Dargonrol/processor-dev/Dragon/Dragon_4/Software/TommyPROM-master/docs/images/TommyPROM-pcb-with-ui.jpg

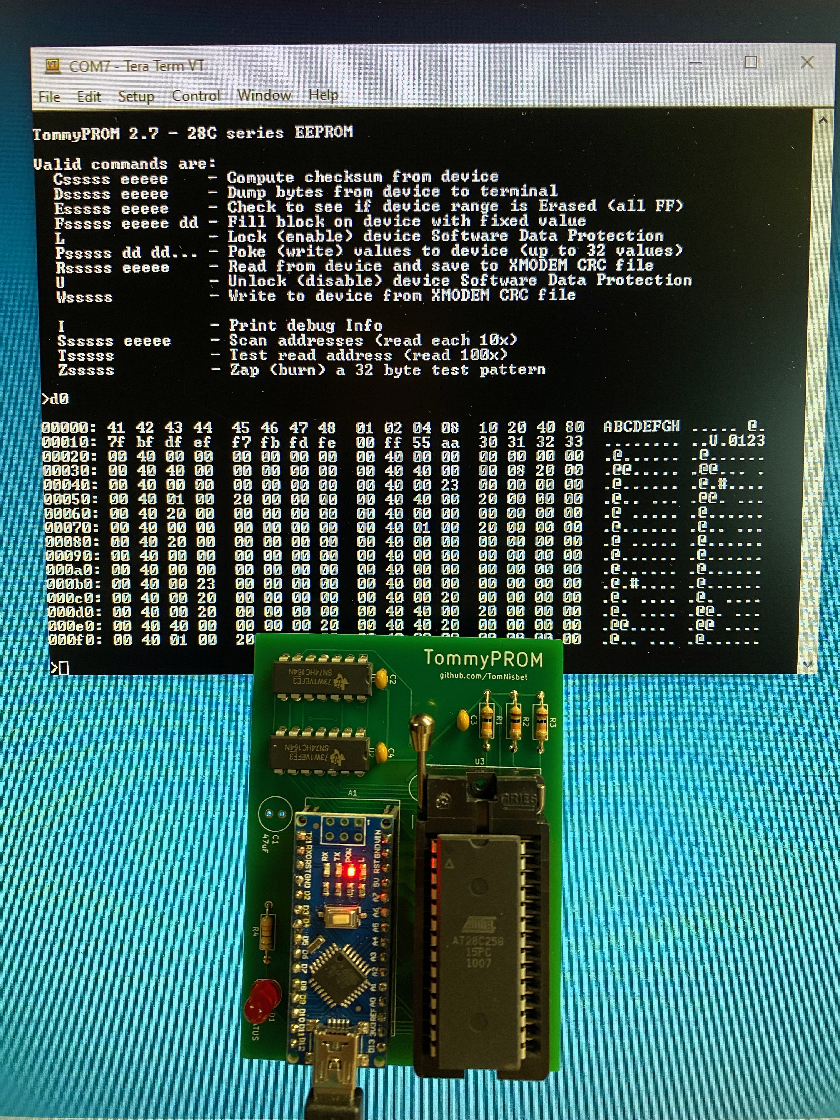
Dragon/Dragon_4/Software/TommyPROM-master/docs/images/TommyPROM-pcb-with-ui.jpg
