Dargonrol/processor-dev/Dragon/Dragon_2/Dragon-2_Microachitecture.JPG

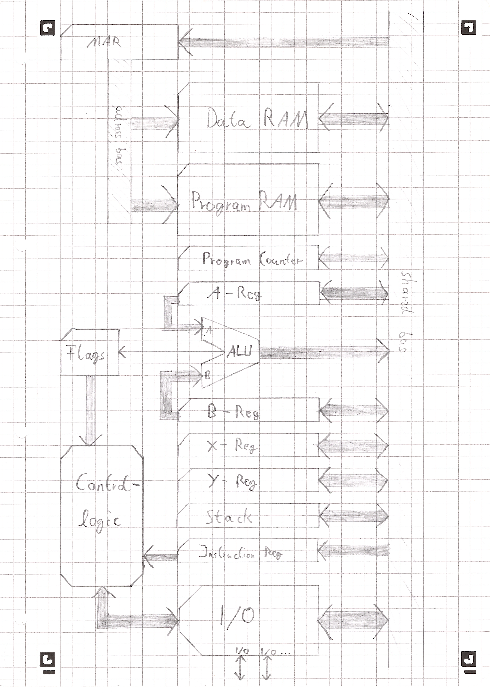
Dragon/Dragon_2/Dragon-2_Microachitecture.JPG
