Dargonrol/processor-dev/Dragon/Dragon_4/Jugend Forscht/Jugend Forscht/Clk-code_screenshot.png

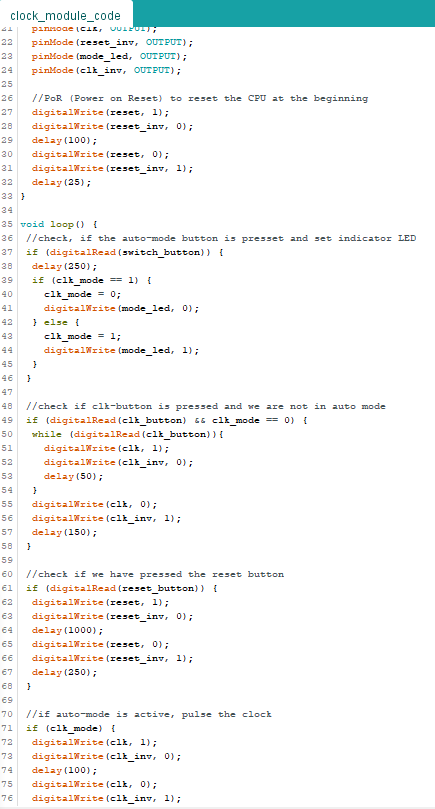
Dragon/Dragon_4/Jugend Forscht/Jugend Forscht/Clk-code_screenshot.png
