Dargonrol/processor-dev/Dragon/Dragon_4/Jugend Forscht/Jugend Forscht/Control-Logic_board_screenshot.png

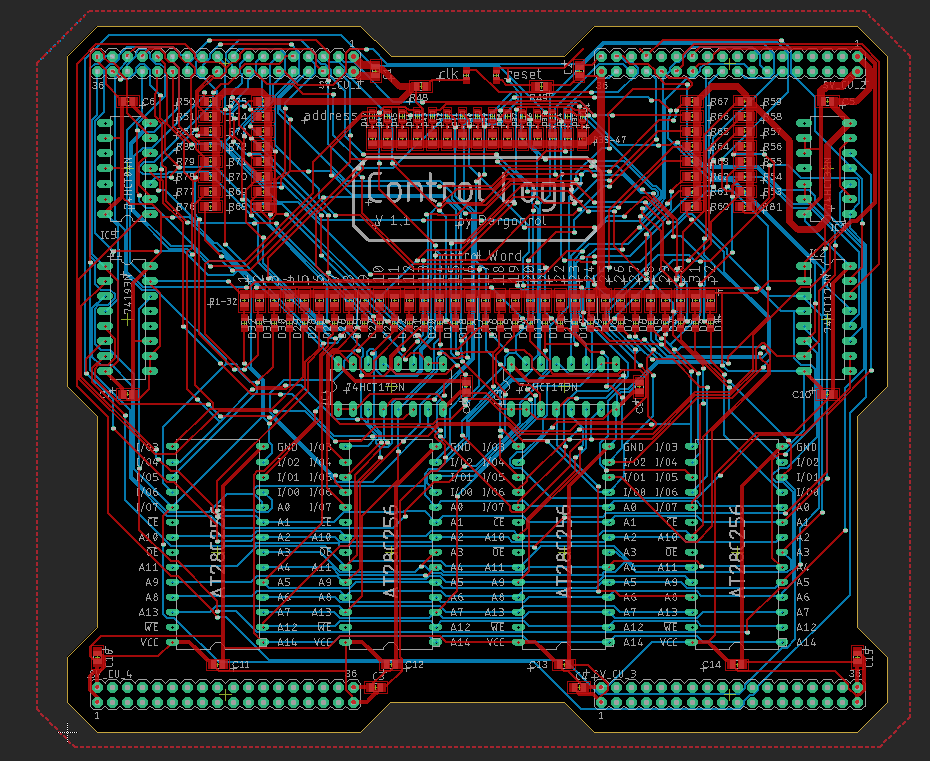
Dragon/Dragon_4/Jugend Forscht/Jugend Forscht/Control-Logic_board_screenshot.png
