Dargonrol/processor-dev/Dragon/Dragon_4/Jugend Forscht/Jugend Forscht/Hex-Editor_screenshot.png

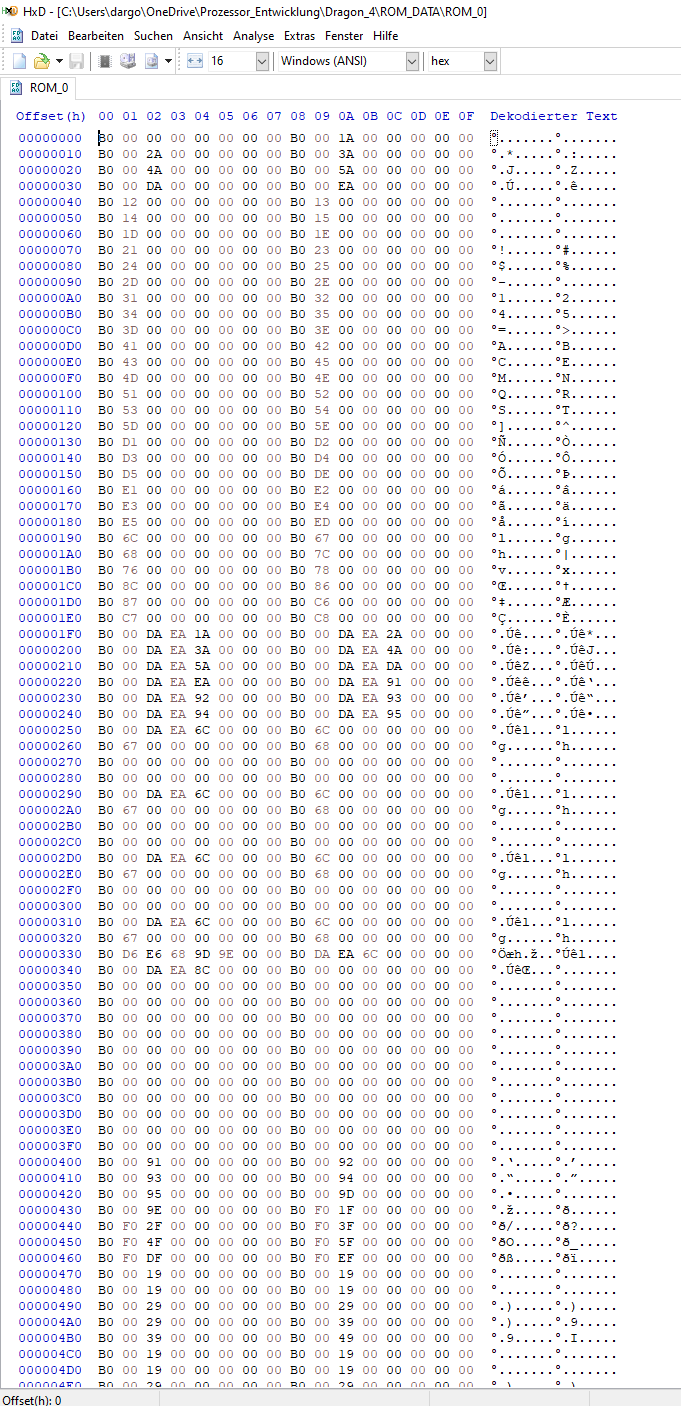
Dragon/Dragon_4/Jugend Forscht/Jugend Forscht/Hex-Editor_screenshot.png
