Dargonrol/processor-dev/Dragon/Dragon_4/Jugend Forscht/Jugend Forscht/logic-simulation_screenshot.png

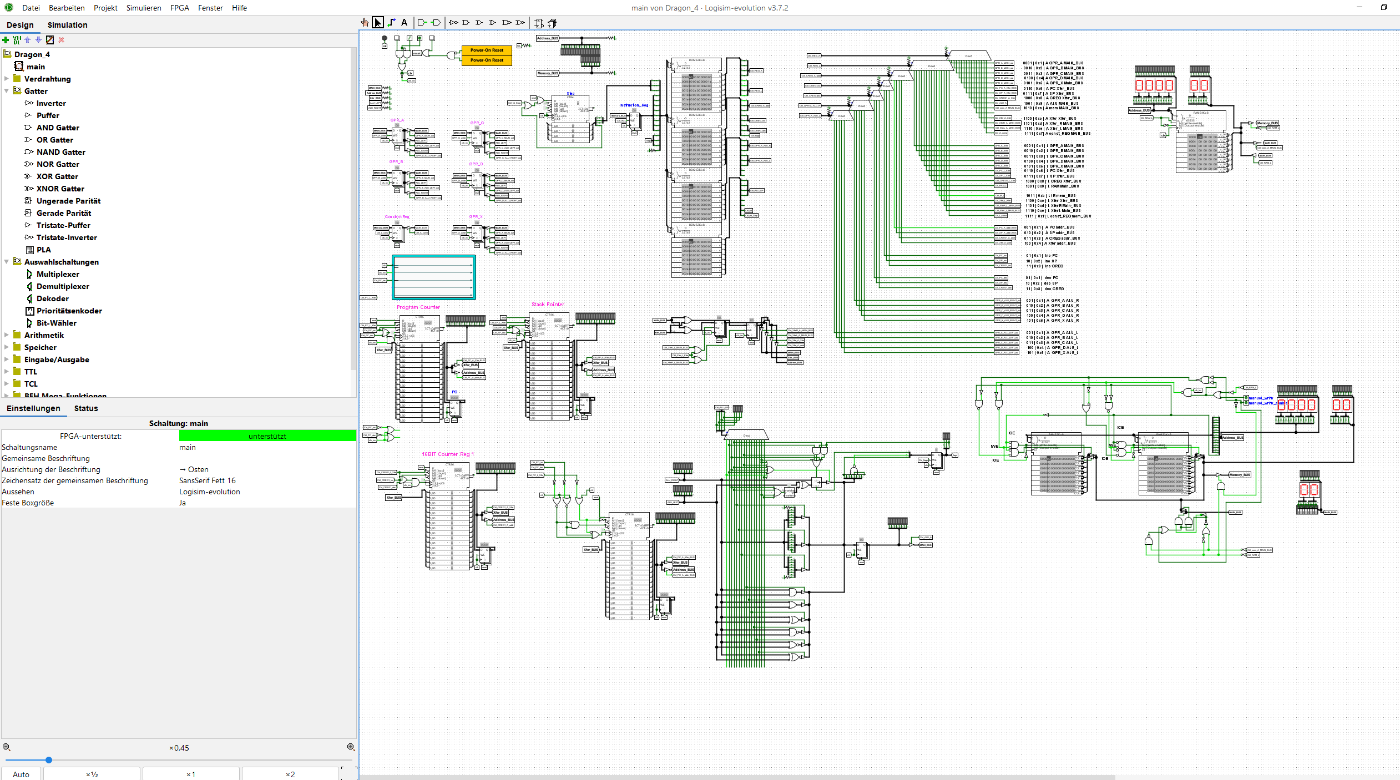
Dragon/Dragon_4/Jugend Forscht/Jugend Forscht/logic-simulation_screenshot.png
