Dargonrol/processor-dev/Dragon/Dragon_4/Jugend Forscht/Jugend Forscht/ROM-Code-gen_1_screenshot.png

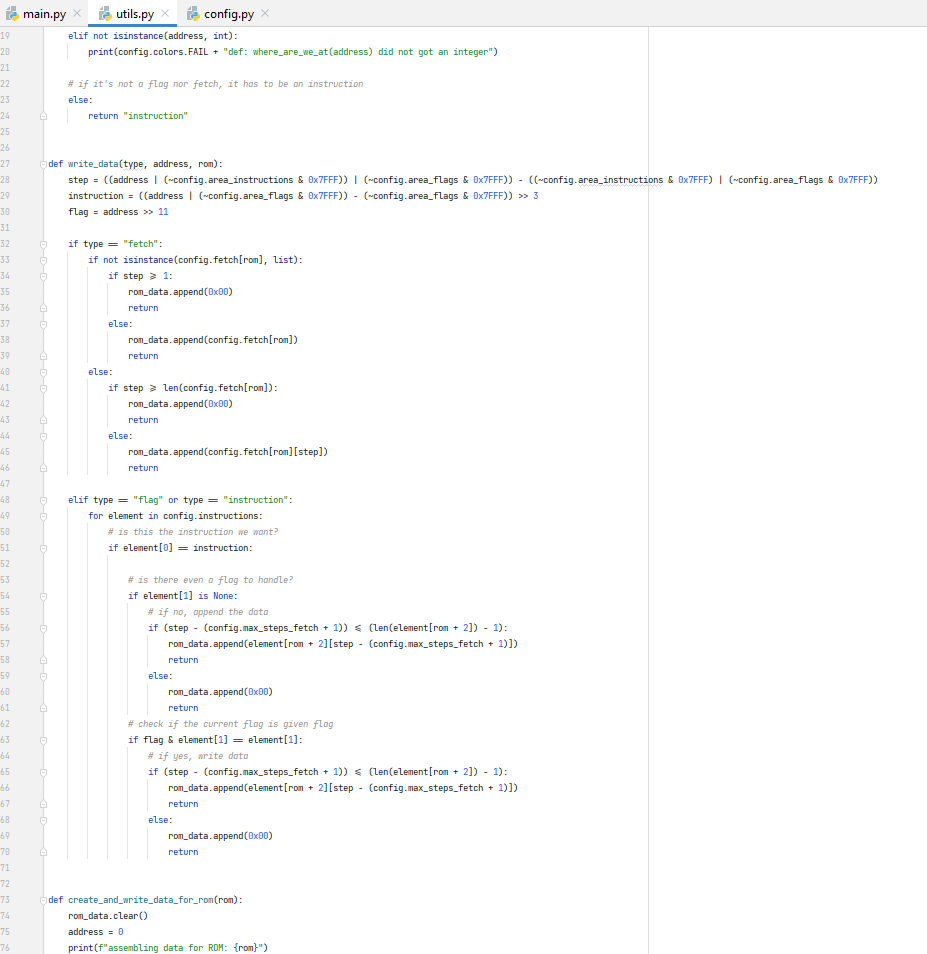
Dragon/Dragon_4/Jugend Forscht/Jugend Forscht/ROM-Code-gen_1_screenshot.png
