Dargonrol/processor-dev/Dragon/Dragon_4/Jugend Forscht/Jugend Forscht/Tera-Term_screenshot.png

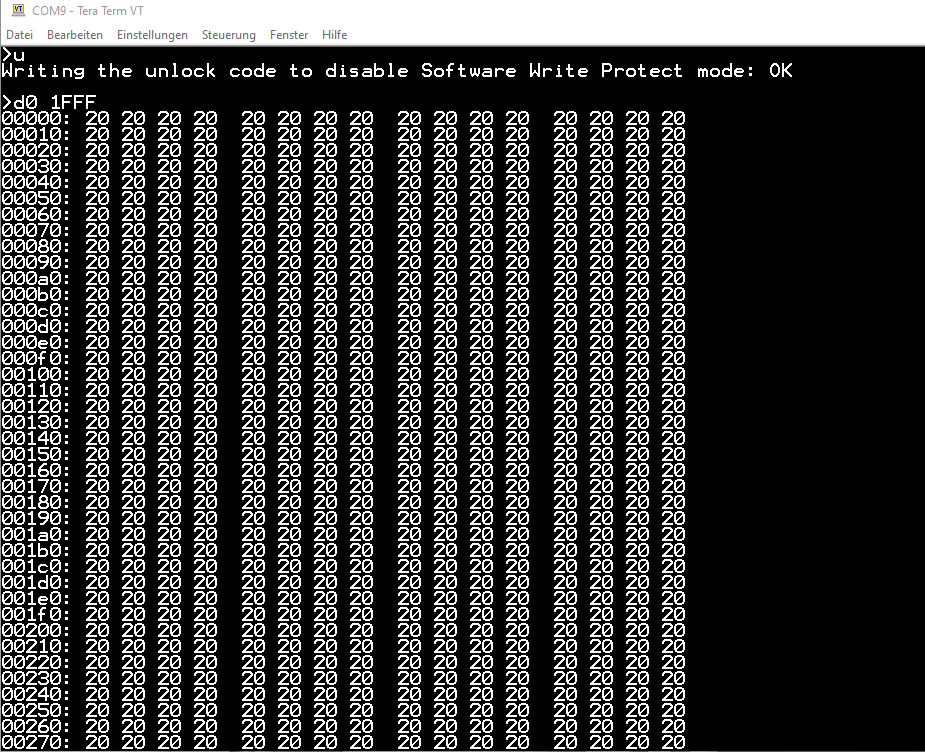
Dragon/Dragon_4/Jugend Forscht/Jugend Forscht/Tera-Term_screenshot.png
