Dargonrol/processor-dev/Dragon/Dragon_4/Software/Control_Logic_Data_generator/temp_screen_1.png

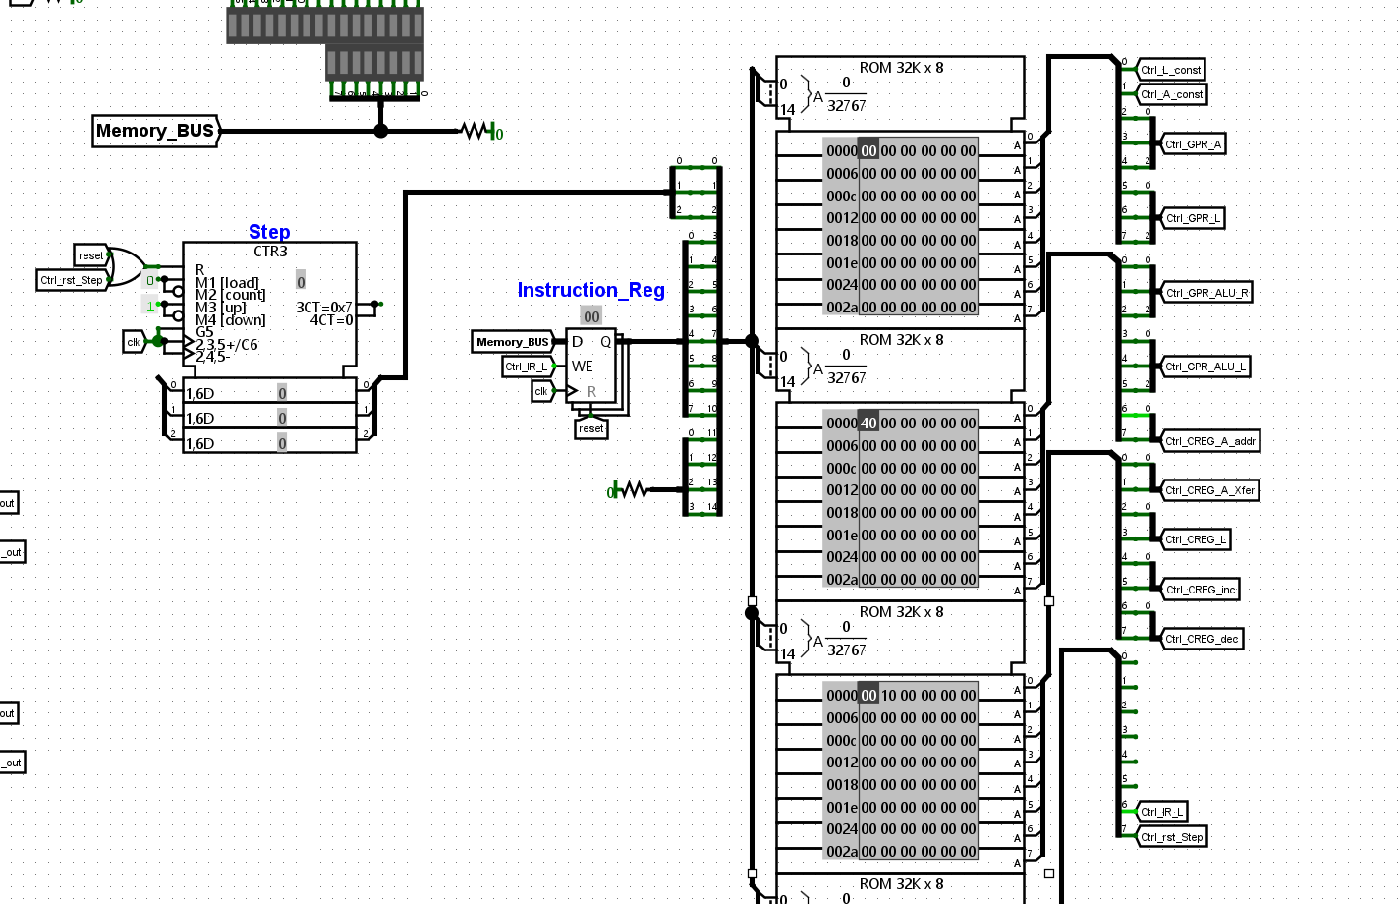
Dragon/Dragon_4/Software/Control_Logic_Data_generator/temp_screen_1.png
