Dargonrol/processor-dev/Dragon/Dragon_4/Jugend Forscht/Jugend Forscht/part_of_instruction-set_definition_screenshot.png

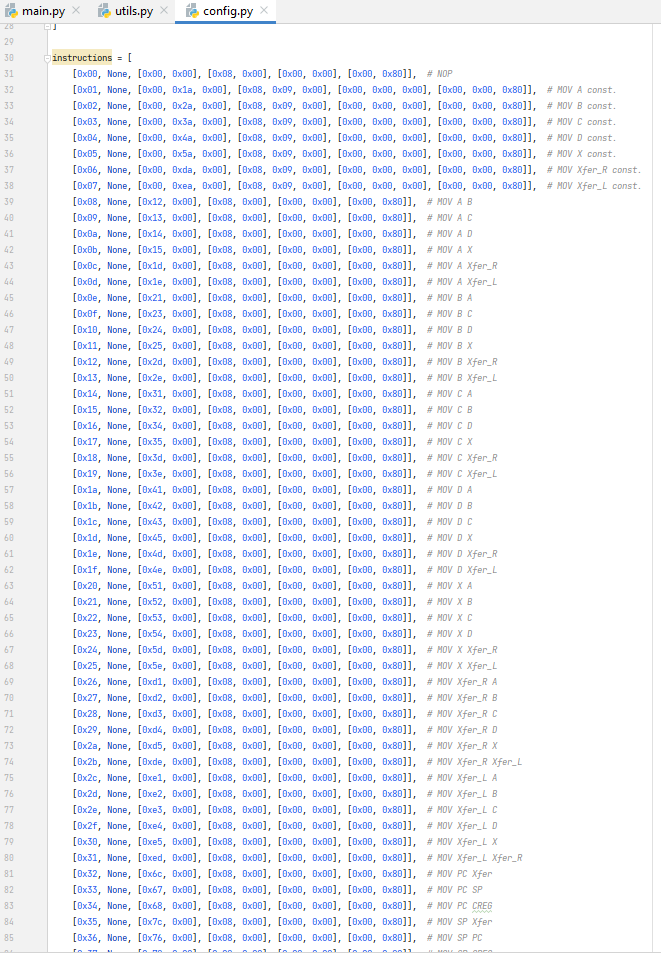
Dragon/Dragon_4/Jugend Forscht/Jugend Forscht/part_of_instruction-set_definition_screenshot.png
