Dargonrol/processor-dev/Dragon/Dragon_4/PCBs/Control Logic/Control_Logic_V2.brd

## EAGLE design Dragon/Dragon_4/PCBs/Control Logic/Control_Logic_V2.brd (2025-08-28)

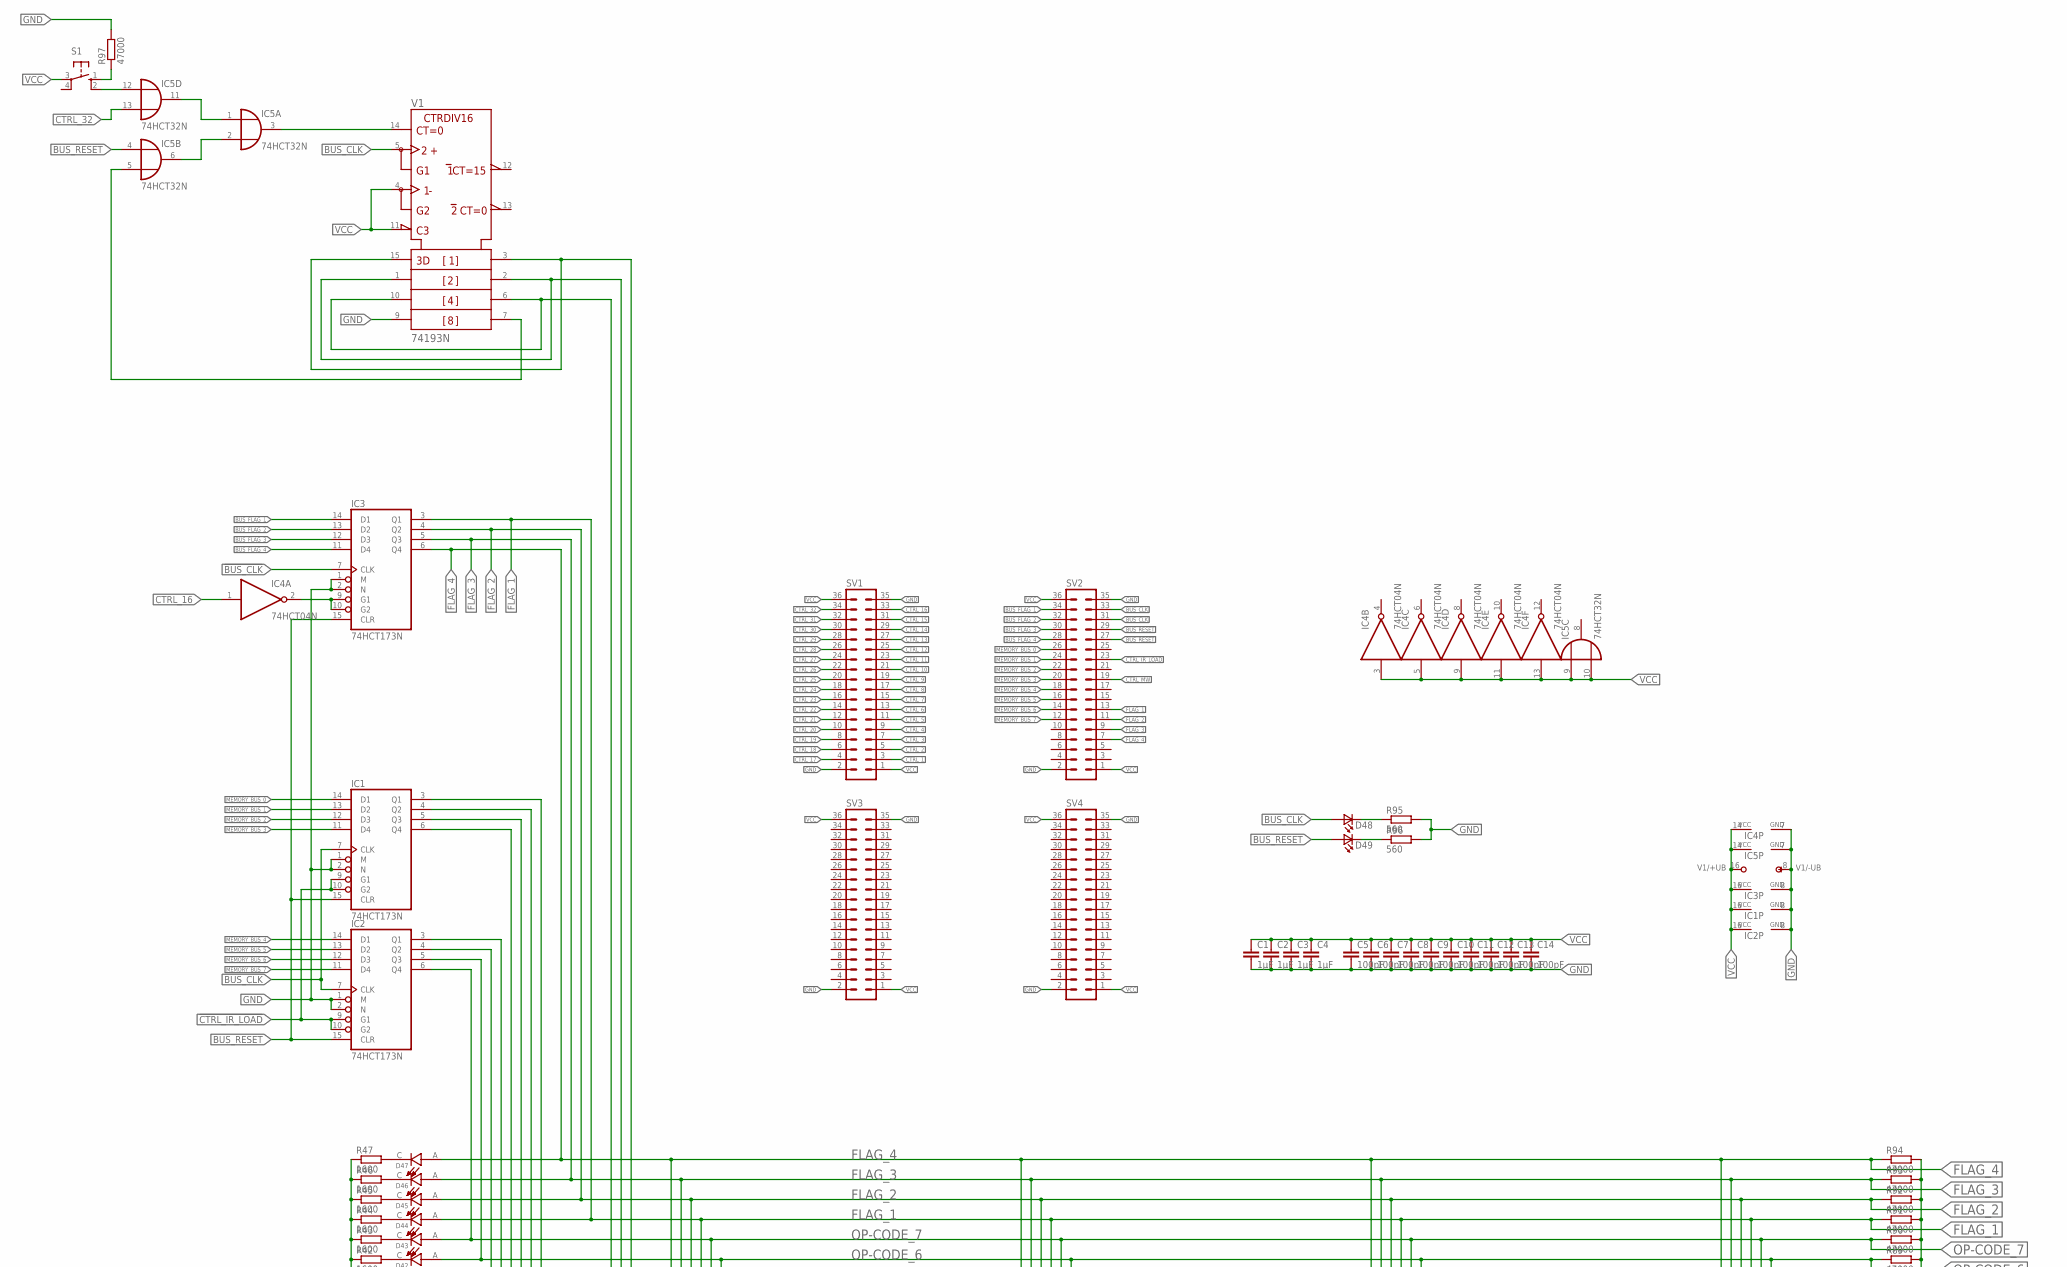
[picture p90: schematic Control_Logic_V2.sch, part in row 1, column 1]

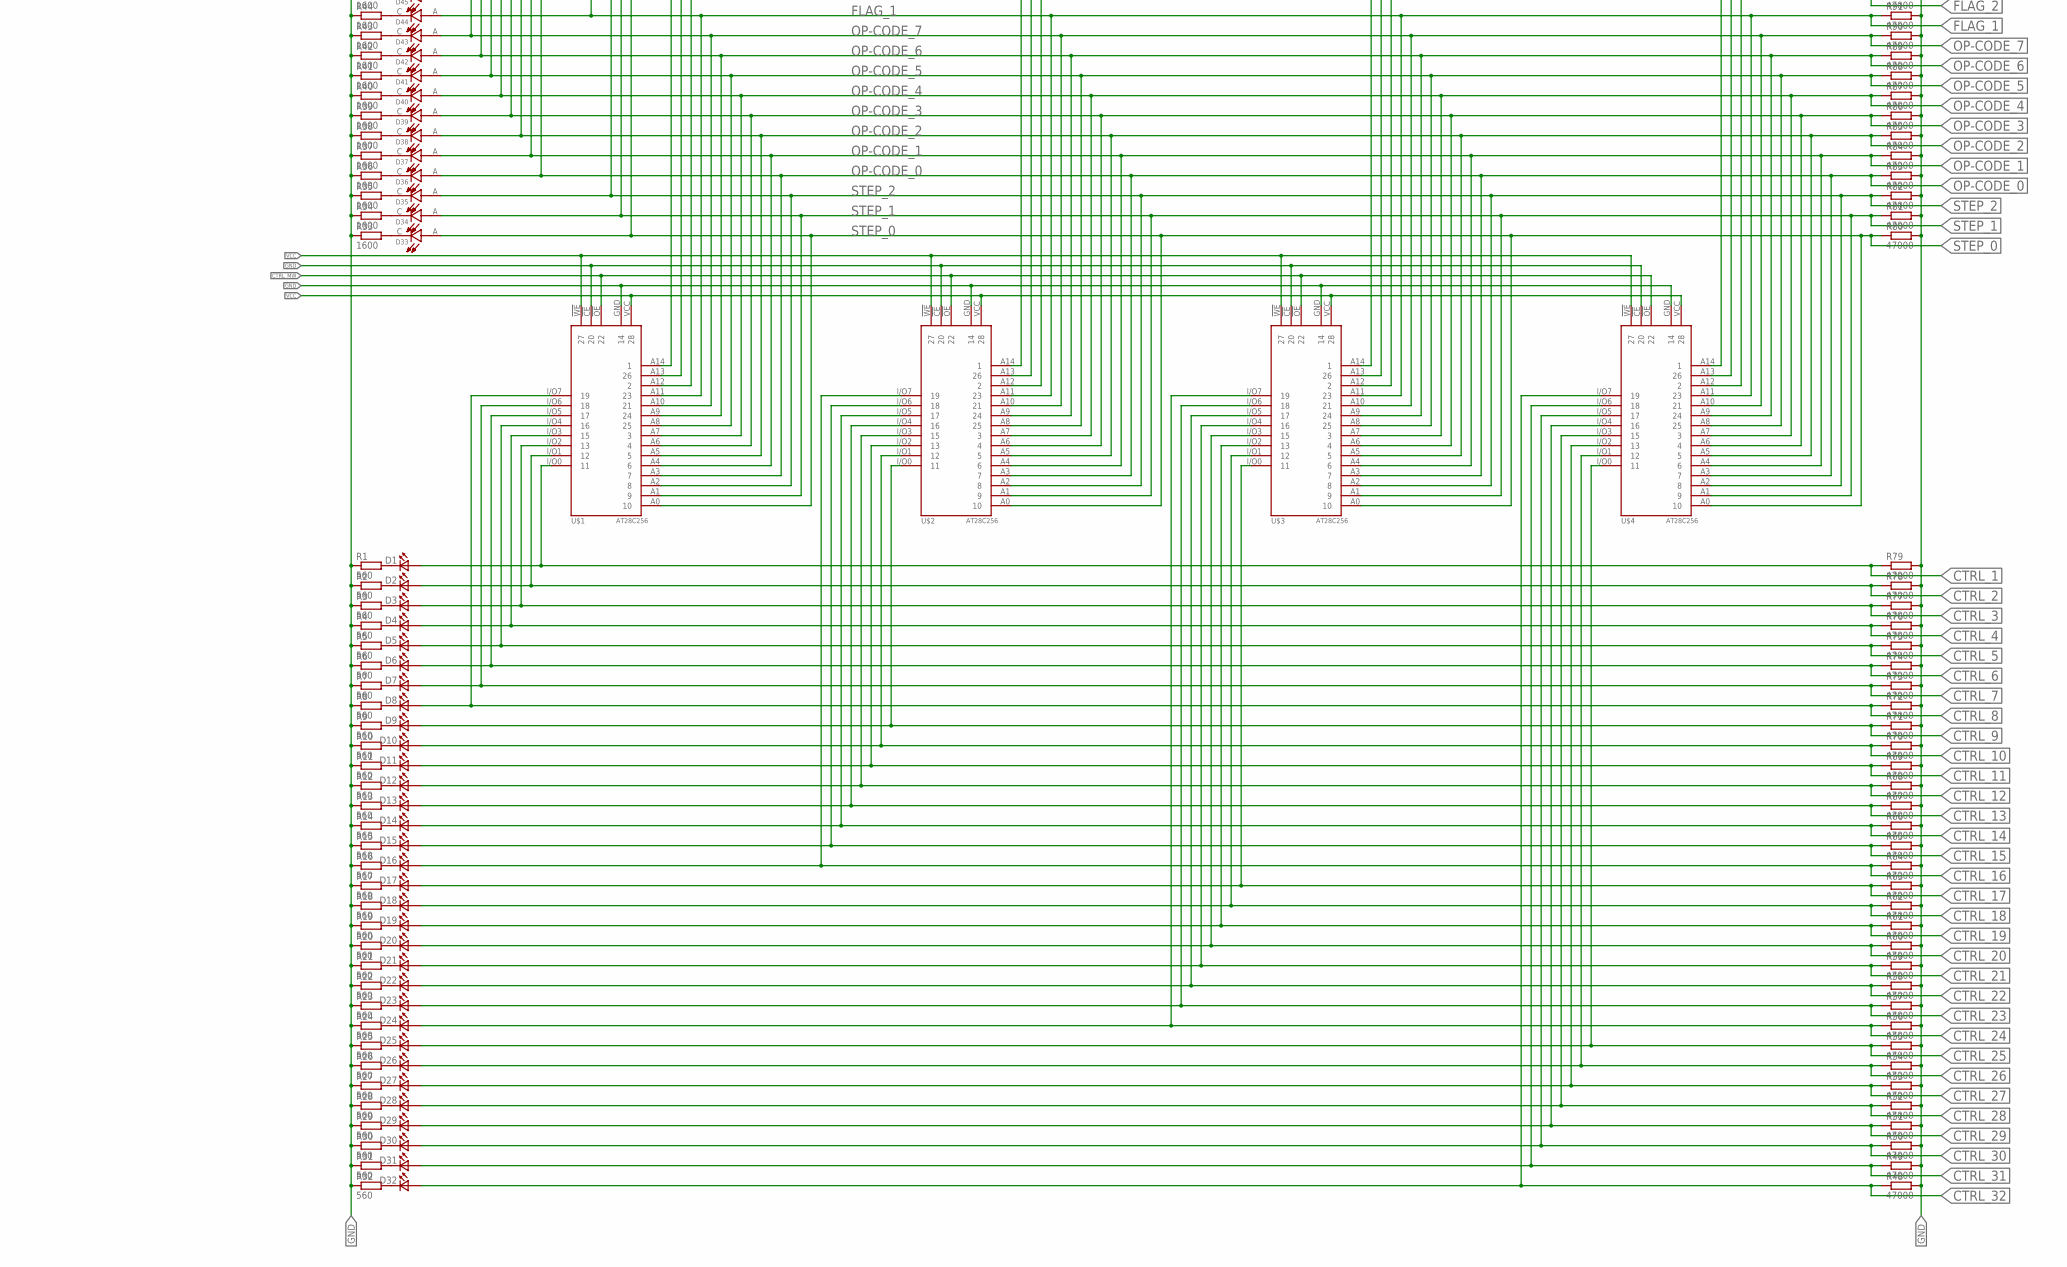
[picture p91: schematic Control_Logic_V2.sch, part in row 2, column 1]

Parts:
C1, C2, C3, C4: 1µF; C0805
C5, C6, C7, C8, C9, C10, C11, C12, C13, C14: 100pF; C0805
D1, D2, D3, D4, D5, D6, D7, D8, D9, D10, D11, D12, D13, D14, D15, D16, D17, D18, D19, D20, D21, D22, D23, D24, D25, D26, D27, D28, D29, D30, D31, D32, D48, D49: LTST-C193TBKT-5A; 0603
D33, D34, D35, D36, D37, D38, D39, D40, D41, D42, D43, D44, D45, D46, D47: LTST-C193KRKT-5A; LEDC1608X45N
IC1, IC2, IC3: 74HCT173N; DIL16
IC4: 74HCT04N; DIL14
IC5: 74HCT32N; DIL14
R1, R2, R3, R4, R5, R6, R7, R8, R9, R10, R11, R12, R13, R14, R15, R16, R17, R18, R19, R20, R21, R22, R23, R24, R25, R26, R27, R28, R29, R30, R31, R32, R95, R96: 560; R0805
R33, R34, R35, R36, R37, R38, R39, R40, R41, R42, R43, R44, R45, R46, R47: 1600; R0805
R48, R49, R50, R51, R52, R53, R54, R55, R56, R57, R58, R59, R60, R61, R62, R63, R64, R65, R66, R67, R68, R69, R70, R71, R72, R73, R74, R75, R76, R77, R78, R79, R80, R81, R82, R83, R84, R85, R86, R87, R88, R89, R90, R91, R92, R93, R94, R97: 47000; R0805
S1: 10-XX; B3F-10XX
SV1, SV2, SV3, SV4: MA18-2
U$1, U$2, U$3, U$4: AT28C256
V1: 74193N; DIL16

Connections:
!BUS_CLK: IC3.7 (CLK), SV2.31
!BUS_RESET: SV2.27
!CTRL_IR_LOAD: IC1.9 (G1), IC1.10 (G2), IC2.9 (G1), IC2.10 (G2), SV2.23
BUS_CLK: D48.2 (A2), IC1.7 (CLK), IC2.7 (CLK), SV2.33, V1.5 (UP)
BUS_FLAG_1: IC3.14 (D1), SV2.34
BUS_FLAG_2: IC3.13 (D2), SV2.32
BUS_FLAG_3: IC3.12 (D3), SV2.30
BUS_FLAG_4: IC3.11 (D4), SV2.28
BUS_RESET: D49.2 (A2), IC1.15 (CLR), IC2.15 (CLR), IC3.15 (CLR), IC5.4 (I0), SV2.29
CTRL_1: D1.2 (A2), R79.1, SV1.3, U$1.I/O0 (11)
CTRL_2: D2.2 (A2), R78.1, SV1.5, U$1.I/O1 (12)
CTRL_3: D3.2 (A2), R77.1, SV1.7, U$1.I/O2 (13)
CTRL_4: D4.2 (A2), R76.1, SV1.9, U$1.I/O3 (15)
CTRL_5: D5.2 (A2), R75.1, SV1.11, U$1.I/O4 (16)
CTRL_6: D6.2 (A2), R74.1, SV1.13, U$1.I/O5 (17)
CTRL_7: D7.2 (A2), R73.1, SV1.15, U$1.I/O6 (18)
CTRL_8: D8.2 (A2), R72.1, SV1.17, U$1.I/O7 (19)
CTRL_9: D9.2 (A2), R71.1, SV1.19, U$2.I/O0 (11)
CTRL_10: D10.2 (A2), R70.1, SV1.21, U$2.I/O1 (12)
CTRL_11: D11.2 (A2), R69.1, SV1.23, U$2.I/O2 (13)
CTRL_12: D12.2 (A2), R68.1, SV1.25, U$2.I/O3 (15)
CTRL_13: D13.2 (A2), R67.1, SV1.27, U$2.I/O4 (16)
CTRL_14: D14.2 (A2), R66.1, SV1.29, U$2.I/O5 (17)
CTRL_15: D15.2 (A2), R65.1, SV1.31, U$2.I/O6 (18)
CTRL_16: D16.2 (A2), IC4.1 (I), R64.1, SV1.33, U$2.I/O7 (19)
CTRL_17: D17.2 (A2), R63.1, SV1.4, U$3.I/O0 (11)
CTRL_18: D18.2 (A2), R62.1, SV1.6, U$3.I/O1 (12)
CTRL_19: D19.2 (A2), R61.1, SV1.8, U$3.I/O2 (13)
CTRL_20: D20.2 (A2), R60.1, SV1.10, U$3.I/O3 (15)
CTRL_21: D21.2 (A2), R59.1, SV1.12, U$3.I/O4 (16)
CTRL_22: D22.2 (A2), R58.1, SV1.14, U$3.I/O5 (17)
CTRL_23: D23.2 (A2), R57.1, SV1.16, U$3.I/O6 (18)
CTRL_24: D24.2 (A2), R56.1, SV1.18, U$3.I/O7 (19)
CTRL_25: D25.2 (A2), R55.1, SV1.20, U$4.I/O0 (11)
CTRL_26: D26.2 (A2), R54.1, SV1.22, U$4.I/O1 (12)
CTRL_27: D27.2 (A2), R53.1, SV1.24, U$4.I/O2 (13)
CTRL_28: D28.2 (A2), R52.1, SV1.26, U$4.I/O3 (15)
CTRL_29: D29.2 (A2), R51.1, SV1.28, U$4.I/O4 (16)
CTRL_30: D30.2 (A2), R50.1, SV1.30, U$4.I/O5 (17)
CTRL_31: D31.2 (A2), R49.1, SV1.32, U$4.I/O6 (18)
CTRL_32: D32.2 (A2), IC5.13 (I1), R48.1, SV1.34, U$4.I/O7 (19)
CTRL_MW: SV2.19, U$1.!OE (22), U$2.!OE (22), U$3.!OE (22), U$4.!OE (22)
FLAG_1: D44.A, IC3.3 (Q1), R91.1, SV2.13, U$1.A11 (23), U$2.A11 (23), U$3.A11 (23), U$4.A11 (23)
FLAG_2: D45.A, IC3.4 (Q2), R92.1, SV2.11, U$1.A12 (2), U$2.A12 (2), U$3.A12 (2), U$4.A12 (2)
FLAG_3: D46.A, IC3.5 (Q3), R93.1, SV2.9, U$1.A13 (26), U$2.A13 (26), U$3.A13 (26), U$4.A13 (26)
FLAG_4: D47.A, IC3.6 (Q4), R94.1, SV2.7, U$1.A14 (1), U$2.A14 (1), U$3.A14 (1), U$4.A14 (1)
GND: C1.2, C2.2, C3.2, C4.2, C5.2, C6.2, C7.2, C8.2, C9.2, C10.2, C11.2, C12.2, C13.2, C14.2, IC1.1 (M), IC1.2 (N), IC1.8 (GND), IC2.1 (M), IC2.2 (N), IC2.8 (GND), IC3.1 (M), IC3.2 (N), IC3.8 (GND), IC4.7 (GND), IC5.7 (GND), R1.1, R2.1, R3.1, R4.1, R5.1, R6.1, R7.1, R8.1, R9.1, R10.1, R11.1, R12.1, R13.1, R14.1, R15.1, R16.1, R17.1, R18.1, R19.1, R20.1, R21.1, R22.1, R23.1, R24.1, R25.1, R26.1, R27.1, R28.1, R29.1, R30.1, R31.1, R32.1, R33.1, R34.1, R35.1, R36.1, R37.1, R38.1, R39.1, R40.1, R41.1, R42.1, R43.1, R44.1, R45.1, R46.1, R47.1, R48.2, R49.2, R50.2, R51.2, R52.2, R53.2, R54.2, R55.2, R56.2, R57.2, R58.2, R59.2, R60.2, R61.2, R62.2, R63.2, R64.2, R65.2, R66.2, R67.2, R68.2, R69.2, R70.2, R71.2, R72.2, R73.2, R74.2, R75.2, R76.2, R77.2, R78.2, R79.2, R80.2, R81.2, R82.2, R83.2, R84.2, R85.2, R86.2, R87.2, R88.2, R89.2, R90.2, R91.2, R92.2, R93.2, R94.2, R95.2, R96.2, R97.2, SV1.2, SV1.35, SV2.2, SV2.35, SV3.2, SV3.35, SV4.2, SV4.35, U$1.!CE (20), U$1.GND (14), U$2.!CE (20), U$2.GND (14), U$3.!CE (20), U$3.GND (14), U$4.!CE (20), U$4.GND (14), V1.8 (-UB), V1.9 (D)
MEMORY_BUS_0: IC1.14 (D1), SV2.26
MEMORY_BUS_1: IC1.13 (D2), SV2.24
MEMORY_BUS_2: IC1.12 (D3), SV2.22
MEMORY_BUS_3: IC1.11 (D4), SV2.20
MEMORY_BUS_4: IC2.14 (D1), SV2.18
MEMORY_BUS_5: IC2.13 (D2), SV2.16
MEMORY_BUS_6: IC2.12 (D3), SV2.14
MEMORY_BUS_7: IC2.11 (D4), SV2.12
unnamed: IC3.9 (G1), IC3.10 (G2), IC4.2 (O)
unnamed: IC5.1 (I0), IC5.11 (O)
unnamed: IC5.2 (I1), IC5.6 (O)
unnamed: IC5.3 (O), V1.14 (CLR)
unnamed: IC5.12 (I0), S1.2 (S1)
unnamed: R97.1, S1.1 (S)
unnamed: IC5.5 (I1), V1.7 (QD)
unnamed: D48.1 (K2), R95.1
unnamed: D49.1 (K2), R96.1
unnamed: D1.1 (K2), R1.2
unnamed: D2.1 (K2), R2.2
unnamed: D3.1 (K2), R3.2
unnamed: D4.1 (K2), R4.2
unnamed: D5.1 (K2), R5.2
unnamed: D6.1 (K2), R6.2
unnamed: D7.1 (K2), R7.2
unnamed: D8.1 (K2), R8.2
unnamed: D9.1 (K2), R9.2
unnamed: D10.1 (K2), R10.2
unnamed: D11.1 (K2), R11.2
unnamed: D12.1 (K2), R12.2
unnamed: D13.1 (K2), R13.2
unnamed: D14.1 (K2), R14.2
unnamed: D15.1 (K2), R15.2
unnamed: D16.1 (K2), R16.2
unnamed: D17.1 (K2), R17.2
unnamed: D18.1 (K2), R18.2
unnamed: D19.1 (K2), R19.2
unnamed: D20.1 (K2), R20.2
unnamed: D21.1 (K2), R21.2
unnamed: D22.1 (K2), R22.2
unnamed: D23.1 (K2), R23.2
unnamed: D24.1 (K2), R24.2
unnamed: D25.1 (K2), R25.2
unnamed: D26.1 (K2), R26.2
unnamed: D27.1 (K2), R27.2
unnamed: D28.1 (K2), R28.2
unnamed: D29.1 (K2), R29.2
unnamed: D30.1 (K2), R30.2
unnamed: D31.1 (K2), R31.2
unnamed: D32.1 (K2), R32.2
unnamed: D33.C, R33.2
unnamed: D34.C, R34.2
unnamed: D35.C, R35.2
unnamed: D36.C, R36.2
unnamed: D37.C, R37.2
unnamed: D38.C, R38.2
unnamed: D39.C, R39.2
unnamed: D40.C, R40.2
unnamed: D41.C, R41.2
unnamed: D42.C, R42.2
unnamed: D43.C, R43.2
unnamed: D44.C, R44.2
unnamed: D45.C, R45.2
unnamed: D46.C, R46.2
unnamed: D47.C, R47.2
OP-CODE_0: D36.A, IC1.3 (Q1), R83.1, U$1.A3 (7), U$2.A3 (7), U$3.A3 (7), U$4.A3 (7)
OP-CODE_1: D37.A, IC1.4 (Q2), R84.1, U$1.A4 (6), U$2.A4 (6), U$3.A4 (6), U$4.A4 (6)
OP-CODE_2: D38.A, IC1.5 (Q3), R85.1, U$1.A5 (5), U$2.A5 (5), U$3.A5 (5), U$4.A5 (5)
OP-CODE_3: D39.A, IC1.6 (Q4), R86.1, U$1.A6 (4), U$2.A6 (4), U$3.A6 (4), U$4.A6 (4)
OP-CODE_4: D40.A, IC2.3 (Q1), R87.1, U$1.A7 (3), U$2.A7 (3), U$3.A7 (3), U$4.A7 (3)
OP-CODE_5: D41.A, IC2.4 (Q2), R88.1, U$1.A8 (25), U$2.A8 (25), U$3.A8 (25), U$4.A8 (25)
OP-CODE_6: D42.A, IC2.5 (Q3), R89.1, U$1.A9 (24), U$2.A9 (24), U$3.A9 (24), U$4.A9 (24)
OP-CODE_7: D43.A, IC2.6 (Q4), R90.1, U$1.A10 (21), U$2.A10 (21), U$3.A10 (21), U$4.A10 (21)
STEP_0: D33.A, R80.1, U$1.A0 (10), U$2.A0 (10), U$3.A0 (10), U$4.A0 (10), V1.3 (QA), V1.15 (A)
STEP_1: D34.A, R81.1, U$1.A1 (9), U$2.A1 (9), U$3.A1 (9), U$4.A1 (9), V1.1 (B), V1.2 (QB)
STEP_2: D35.A, R82.1, U$1.A2 (8), U$2.A2 (8), U$3.A2 (8), U$4.A2 (8), V1.6 (QC), V1.10 (C)
VCC: C1.1, C2.1, C3.1, C4.1, C5.1, C6.1, C7.1, C8.1, C9.1, C10.1, C11.1, C12.1, C13.1, C14.1, IC1.16 (VCC), IC2.16 (VCC), IC3.16 (VCC), IC4.3 (I), IC4.5 (I), IC4.9 (I), IC4.11 (I), IC4.13 (I), IC4.14 (VCC), IC5.9 (I0), IC5.10 (I1), IC5.14 (VCC), S1.3, SV1.1, SV1.36, SV2.1, SV2.36, SV3.1, SV3.36, SV4.1, SV4.36, U$1.!WE (27), U$1.VCC (28), U$2.!WE (27), U$2.VCC (28), U$3.!WE (27), U$3.VCC (28), U$4.!WE (27), U$4.VCC (28), V1.4 (DOWN), V1.11 (!LOAD), V1.16 (+UB)

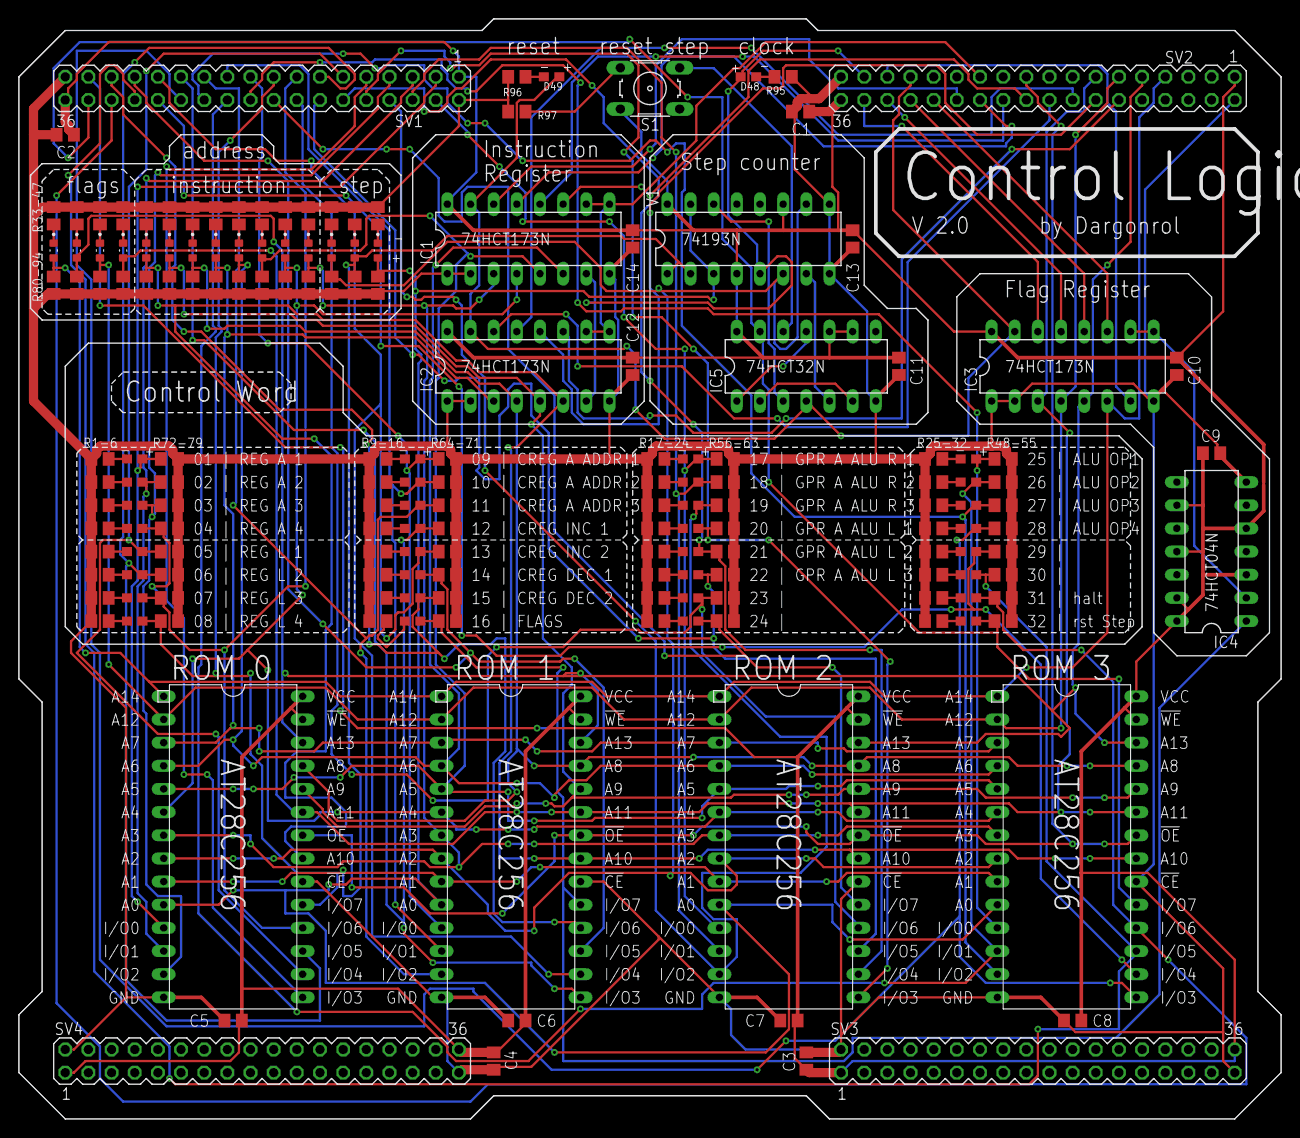
[picture p92: board Control_Logic_V2.brd from above]

Board: 2 copper layers, 138.4 x 120.7 mm, 175 parts (0 on the bottom side), 122 nets.
