Dargonrol/processor-dev/Dragon/Dragon_4/PCBs/Control Logic/Control_Logic.brd

## EAGLE design Dragon/Dragon_4/PCBs/Control Logic/Control_Logic.brd (continued)

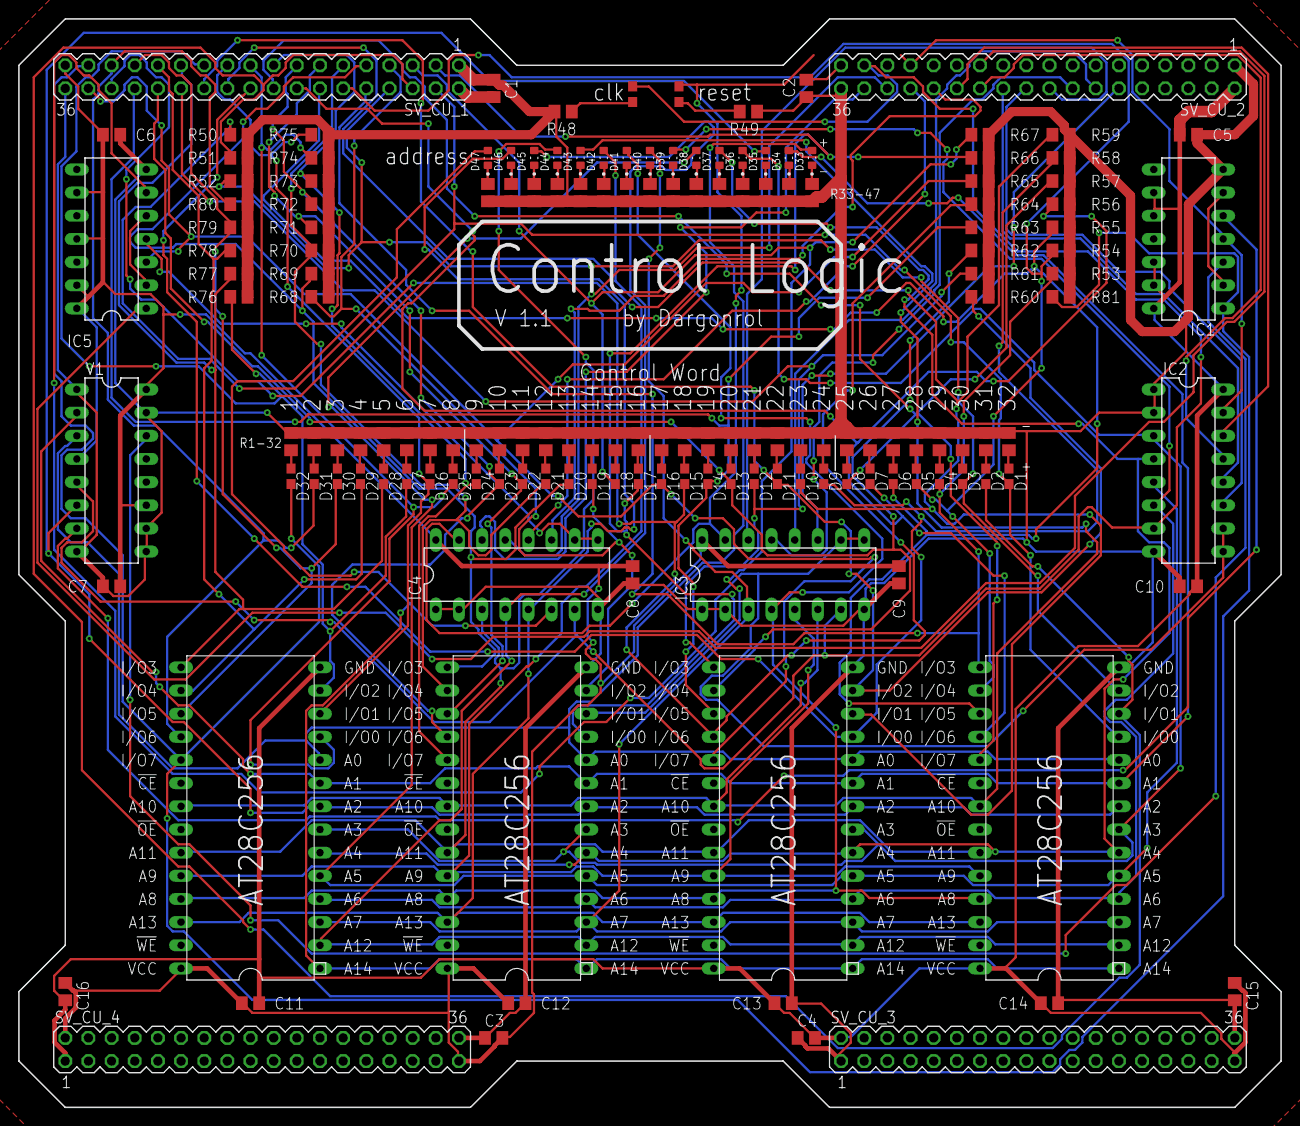
[picture p95: board Control_Logic.brd from above]

Board: 2 copper layers, 138.4 x 119.4 mm, 160 parts (0 on the bottom side), 119 nets.
