Dargonrol/processor-dev/Dragon/Dragon_4/PCBs/GPRs/GPR.brd

## EAGLE design Dragon/Dragon_4/PCBs/GPRs/GPR.brd (2025-08-28)

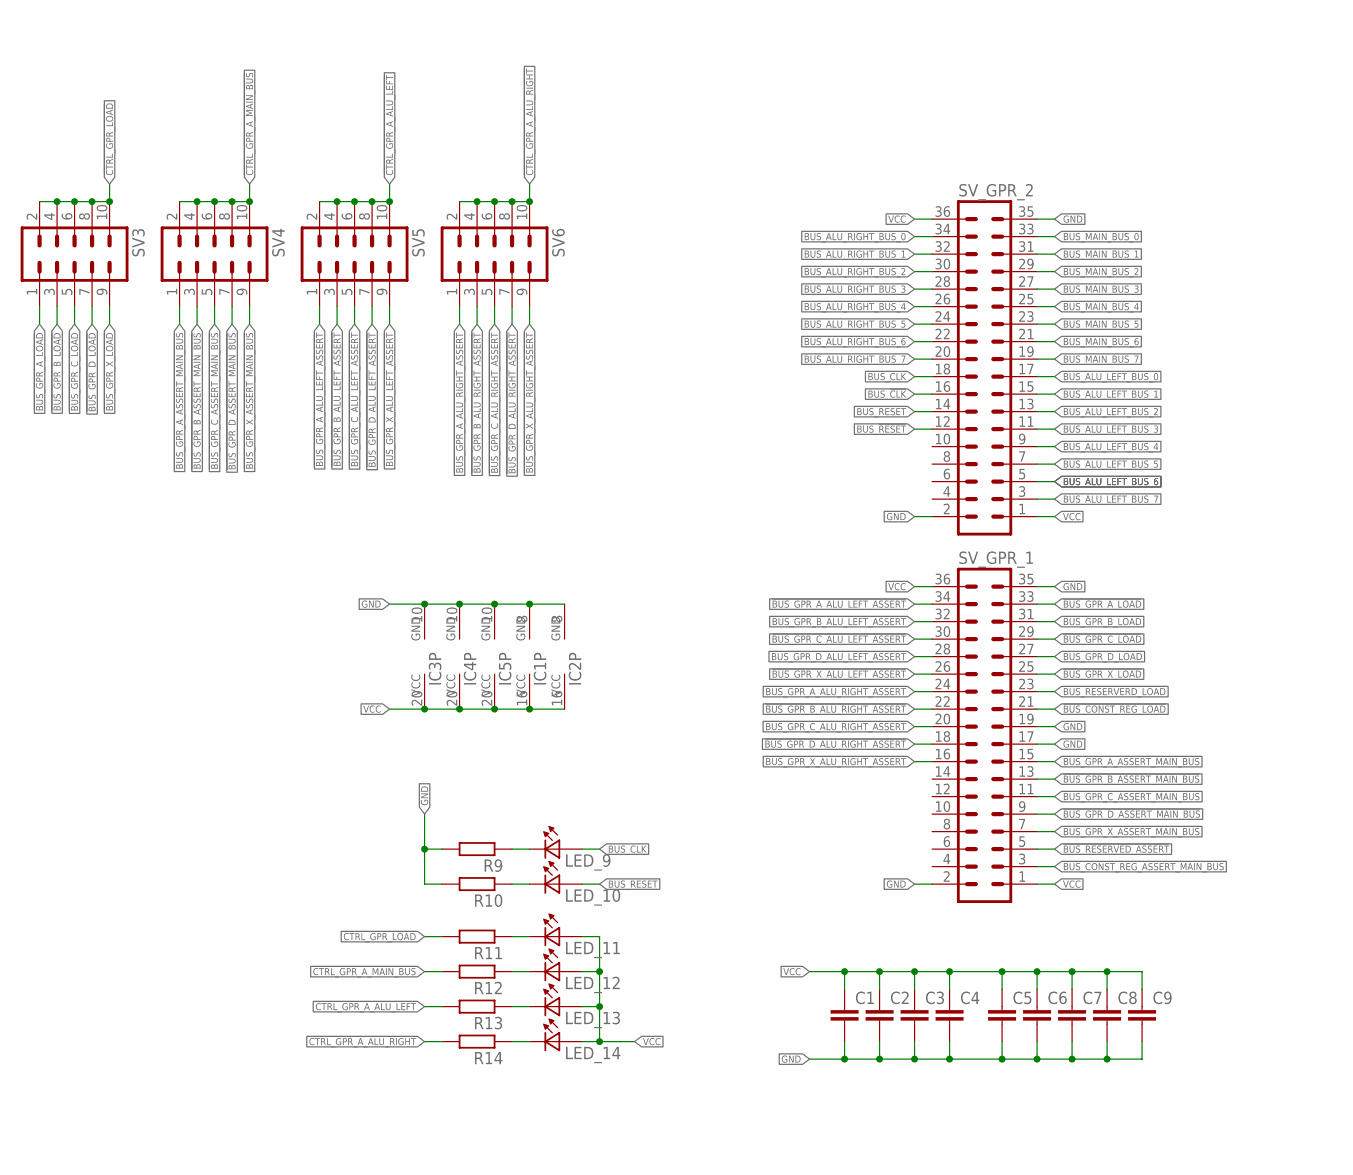
[picture p96: schematic GPR.sch, part in row 1, column 1]

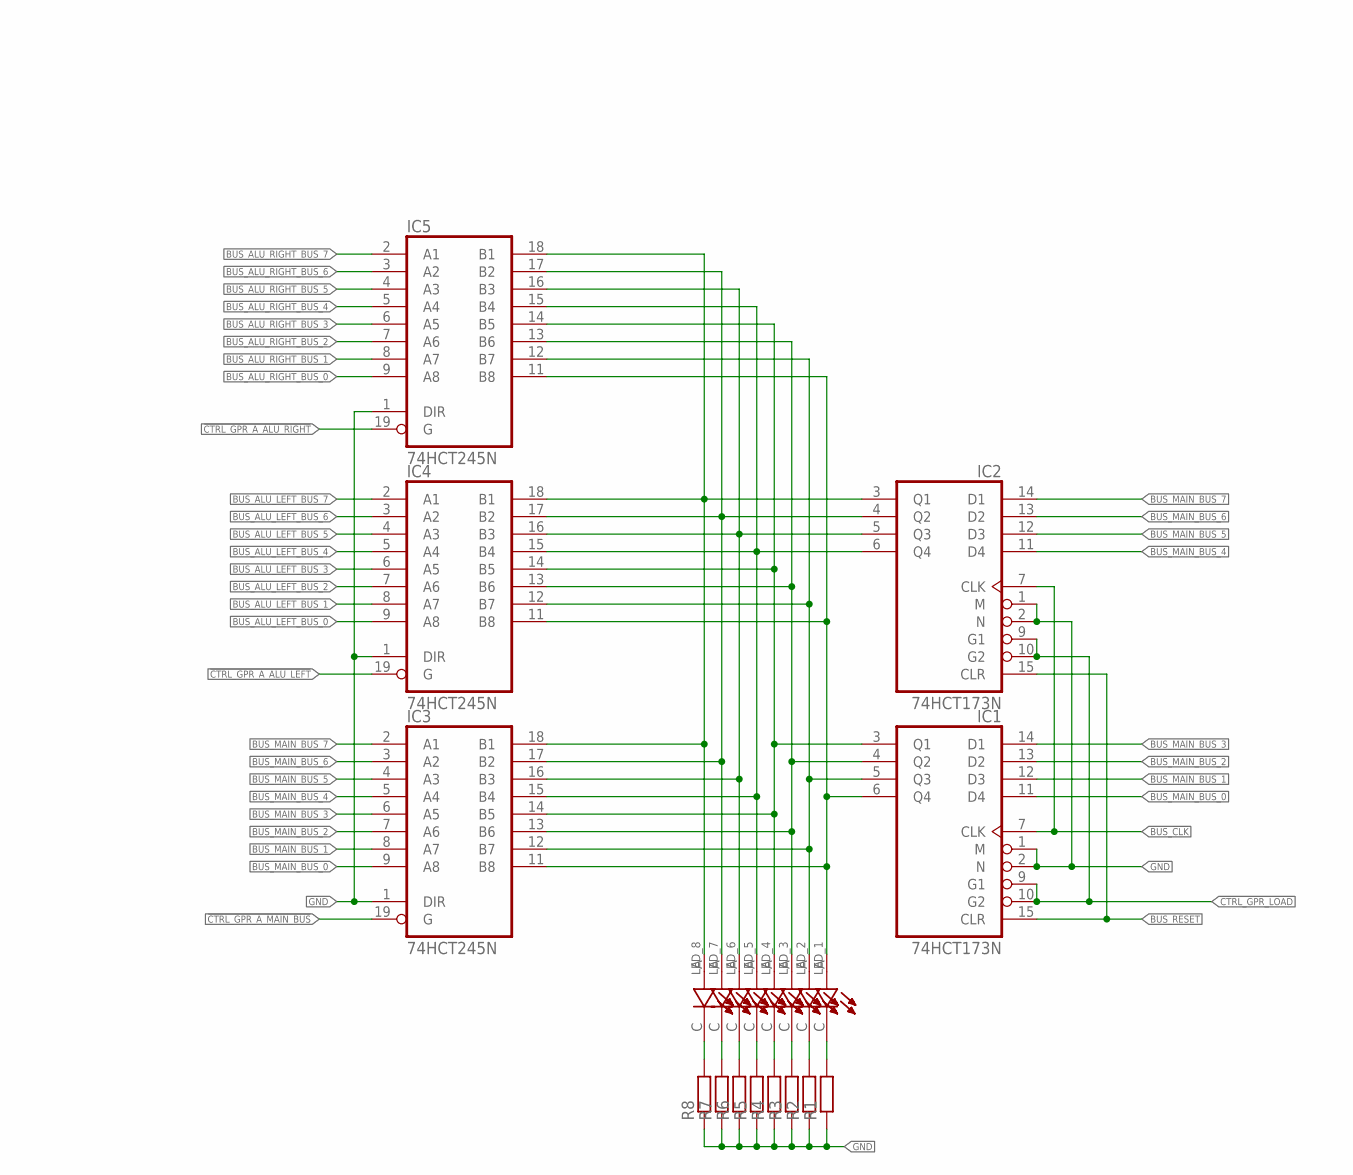
[picture p97: schematic GPR.sch, part in row 1, column 2]

Parts:
C1, C2, C3, C4, C5, C6, C7, C8, C9: C-EUC0805; C0805
IC1, IC2: 74HCT173N; DIL16
IC3, IC4, IC5: 74HCT245N; DIL20
LED_1, LED_2, LED_3, LED_4, LED_5, LED_6, LED_7, LED_8: LTST-C193KRKT-5A; LEDC1608X45N
LED_9, LED_10, LED_11, LED_12, LED_13, LED_14: LTST-C193TBKT-5A; 0603
R1, R2, R3, R4, R5, R6, R7, R8, R9, R10, R11, R12, R13, R14: R-EU_R0805; R0805
SV3, SV4, SV5, SV6: MA05-2
SV_GPR_1, SV_GPR_2: MA18-2

Connections:
!BUS_CONST_REG_ASSERT_MAIN_BUS: SV_GPR_1.3
!BUS_CONST_REG_LOAD: SV_GPR_1.21
!BUS_GPR_A_ALU_LEFT_ASSERT: SV5.1, SV_GPR_1.34
!BUS_GPR_A_ALU_RIGHT_ASSERT: SV6.1, SV_GPR_1.24
!BUS_GPR_A_ASSERT_MAIN_BUS: SV4.1, SV_GPR_1.15
!BUS_GPR_A_LOAD: SV3.1, SV_GPR_1.33
!BUS_GPR_B_ALU_LEFT_ASSERT: SV5.3, SV_GPR_1.32
!BUS_GPR_B_ALU_RIGHT_ASSERT: SV6.3, SV_GPR_1.22
!BUS_GPR_B_ASSERT_MAIN_BUS: SV4.3, SV_GPR_1.13
!BUS_GPR_B_LOAD: SV3.3, SV_GPR_1.31
!BUS_GPR_C_ALU_LEFT_ASSERT: SV5.5, SV_GPR_1.30
!BUS_GPR_C_ALU_RIGHT_ASSERT: SV6.5, SV_GPR_1.20
!BUS_GPR_C_ASSERT_MAIN_BUS: SV4.5, SV_GPR_1.11
!BUS_GPR_C_LOAD: SV3.5, SV_GPR_1.29
!BUS_GPR_D_ALU_LEFT_ASSERT: SV5.7, SV_GPR_1.28
!BUS_GPR_D_ALU_RIGHT_ASSERT: SV6.7, SV_GPR_1.18
!BUS_GPR_D_ASSERT_MAIN_BUS: SV4.7, SV_GPR_1.9
!BUS_GPR_D_LOAD: SV3.7, SV_GPR_1.27
!BUS_GPR_X_ALU_LEFT_ASSERT: SV5.9, SV_GPR_1.26
!BUS_GPR_X_ALU_RIGHT_ASSERT: SV6.9, SV_GPR_1.16
!BUS_GPR_X_ASSERT_MAIN_BUS: SV4.9, SV_GPR_1.7
!BUS_GPR_X_LOAD: SV3.9, SV_GPR_1.25
!BUS_RESERVED_ASSERT: SV_GPR_1.5
!BUS_RESERVERD_LOAD: SV_GPR_1.23
!CTRL_GPR_A_ALU_LEFT: IC4.19 (G), R13.2, SV5.2, SV5.4, SV5.6, SV5.8, SV5.10
!CTRL_GPR_A_ALU_RIGHT: IC5.19 (G), R14.2, SV6.2, SV6.4, SV6.6, SV6.8, SV6.10
!CTRL_GPR_A_MAIN_BUS: IC3.19 (G), R12.2, SV4.2, SV4.4, SV4.6, SV4.8, SV4.10
!CTRL_GPR_LOAD: IC1.9 (G1), IC1.10 (G2), IC2.9 (G1), IC2.10 (G2), R11.2, SV3.2, SV3.4, SV3.6, SV3.8, SV3.10
BUS_!CLK: IC1.7 (CLK), IC2.7 (CLK), SV_GPR_2.16
BUS_!RESET: SV_GPR_2.12
BUS_ALU_LEFT_BUS_0: IC4.9 (A8), SV_GPR_2.17
BUS_ALU_LEFT_BUS_1: IC4.8 (A7), SV_GPR_2.15
BUS_ALU_LEFT_BUS_2: IC4.7 (A6), SV_GPR_2.13
BUS_ALU_LEFT_BUS_3: IC4.6 (A5), SV_GPR_2.11
BUS_ALU_LEFT_BUS_4: IC4.5 (A4), SV_GPR_2.9
BUS_ALU_LEFT_BUS_5: IC4.4 (A3), SV_GPR_2.7
BUS_ALU_LEFT_BUS_6: IC4.3 (A2), SV_GPR_2.5
BUS_ALU_LEFT_BUS_7: IC4.2 (A1), SV_GPR_2.3
BUS_ALU_RIGHT_BUS_0: IC5.9 (A8), SV_GPR_2.34
BUS_ALU_RIGHT_BUS_1: IC5.8 (A7), SV_GPR_2.32
BUS_ALU_RIGHT_BUS_2: IC5.7 (A6), SV_GPR_2.30
BUS_ALU_RIGHT_BUS_3: IC5.6 (A5), SV_GPR_2.28
BUS_ALU_RIGHT_BUS_4: IC5.5 (A4), SV_GPR_2.26
BUS_ALU_RIGHT_BUS_5: IC5.4 (A3), SV_GPR_2.24
BUS_ALU_RIGHT_BUS_6: IC5.3 (A2), SV_GPR_2.22
BUS_ALU_RIGHT_BUS_7: IC5.2 (A1), SV_GPR_2.20
BUS_CLK: LED_9.2 (A2), SV_GPR_2.18
BUS_MAIN_BUS_0: IC1.11 (D4), IC3.9 (A8), SV_GPR_2.33
BUS_MAIN_BUS_1: IC1.12 (D3), IC3.8 (A7), SV_GPR_2.31
BUS_MAIN_BUS_2: IC1.13 (D2), IC3.7 (A6), SV_GPR_2.29
BUS_MAIN_BUS_3: IC1.14 (D1), IC3.6 (A5), SV_GPR_2.27
BUS_MAIN_BUS_4: IC2.11 (D4), IC3.5 (A4), SV_GPR_2.25
BUS_MAIN_BUS_5: IC2.12 (D3), IC3.4 (A3), SV_GPR_2.23
BUS_MAIN_BUS_6: IC2.13 (D2), IC3.3 (A2), SV_GPR_2.21
BUS_MAIN_BUS_7: IC2.14 (D1), IC3.2 (A1), SV_GPR_2.19
BUS_RESET: IC1.15 (CLR), IC2.15 (CLR), LED_10.2 (A2), SV_GPR_2.14
GND: C1.2, C2.2, C3.2, C4.2, C5.2, C6.2, C7.2, C8.2, C9.2, IC1.1 (M), IC1.2 (N), IC1.8 (GND), IC2.1 (M), IC2.2 (N), IC2.8 (GND), IC3.1 (DIR), IC3.10 (GND), IC4.1 (DIR), IC4.10 (GND), IC5.1 (DIR), IC5.10 (GND), R1.1, R2.1, R3.1, R4.1, R5.1, R6.1, R7.1, R8.1, R9.2, R10.2, SV_GPR_1.2, SV_GPR_1.17, SV_GPR_1.19, SV_GPR_1.35, SV_GPR_2.2, SV_GPR_2.35
unnamed: LED_9.1 (K2), R9.1
unnamed: LED_10.1 (K2), R10.1
unnamed: LED_11.1 (K2), R11.1
unnamed: LED_12.1 (K2), R12.1
unnamed: LED_13.1 (K2), R13.1
unnamed: LED_1.C, R1.2
unnamed: LED_2.C, R2.2
unnamed: LED_3.C, R3.2
unnamed: LED_4.C, R4.2
unnamed: LED_5.C, R5.2
unnamed: LED_6.C, R6.2
unnamed: LED_7.C, R7.2
unnamed: LED_8.C, R8.2
unnamed: LED_14.1 (K2), R14.1
unnamed: IC1.3 (Q1), IC3.14 (B5), IC4.14 (B5), IC5.14 (B5), LED_4.A
unnamed: IC2.4 (Q2), IC3.17 (B2), IC4.17 (B2), IC5.17 (B2), LED_7.A
unnamed: IC2.6 (Q4), IC3.15 (B4), IC4.15 (B4), IC5.15 (B4), LED_5.A
unnamed: IC2.5 (Q3), IC3.16 (B3), IC4.16 (B3), IC5.16 (B3), LED_6.A
unnamed: IC1.6 (Q4), IC3.11 (B8), IC4.11 (B8), IC5.11 (B8), LED_1.A
unnamed: IC1.5 (Q3), IC3.12 (B7), IC4.12 (B7), IC5.12 (B7), LED_2.A
unnamed: IC1.4 (Q2), IC3.13 (B6), IC4.13 (B6), IC5.13 (B6), LED_3.A
unnamed: IC2.3 (Q1), IC3.18 (B1), IC4.18 (B1), IC5.18 (B1), LED_8.A
VCC: C1.1, C2.1, C3.1, C4.1, C5.1, C6.1, C7.1, C8.1, C9.1, IC1.16 (VCC), IC2.16 (VCC), IC3.20 (VCC), IC4.20 (VCC), IC5.20 (VCC), LED_11.2 (A2), LED_12.2 (A2), LED_13.2 (A2), LED_14.2 (A2), SV_GPR_1.1, SV_GPR_1.36, SV_GPR_2.1, SV_GPR_2.36

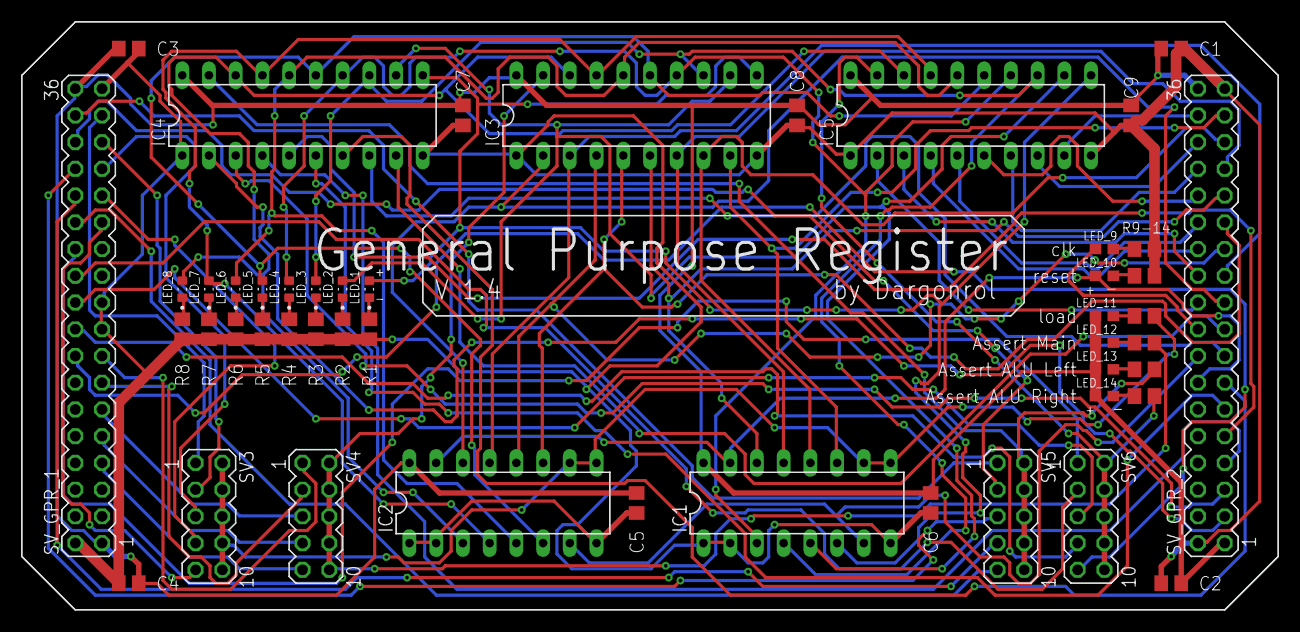
[picture p98: board GPR.brd from above]

Board: 2 copper layers, 119.4 x 55.9 mm, 48 parts (0 on the bottom side), 75 nets.
