Dargonrol/processor-dev/Dragon/Dragon_4/PCBs/Main Board/Mainboard_RIGHT.brd

## EAGLE design Dragon/Dragon_4/PCBs/Main Board/Mainboard_RIGHT.brd (2025-08-28)

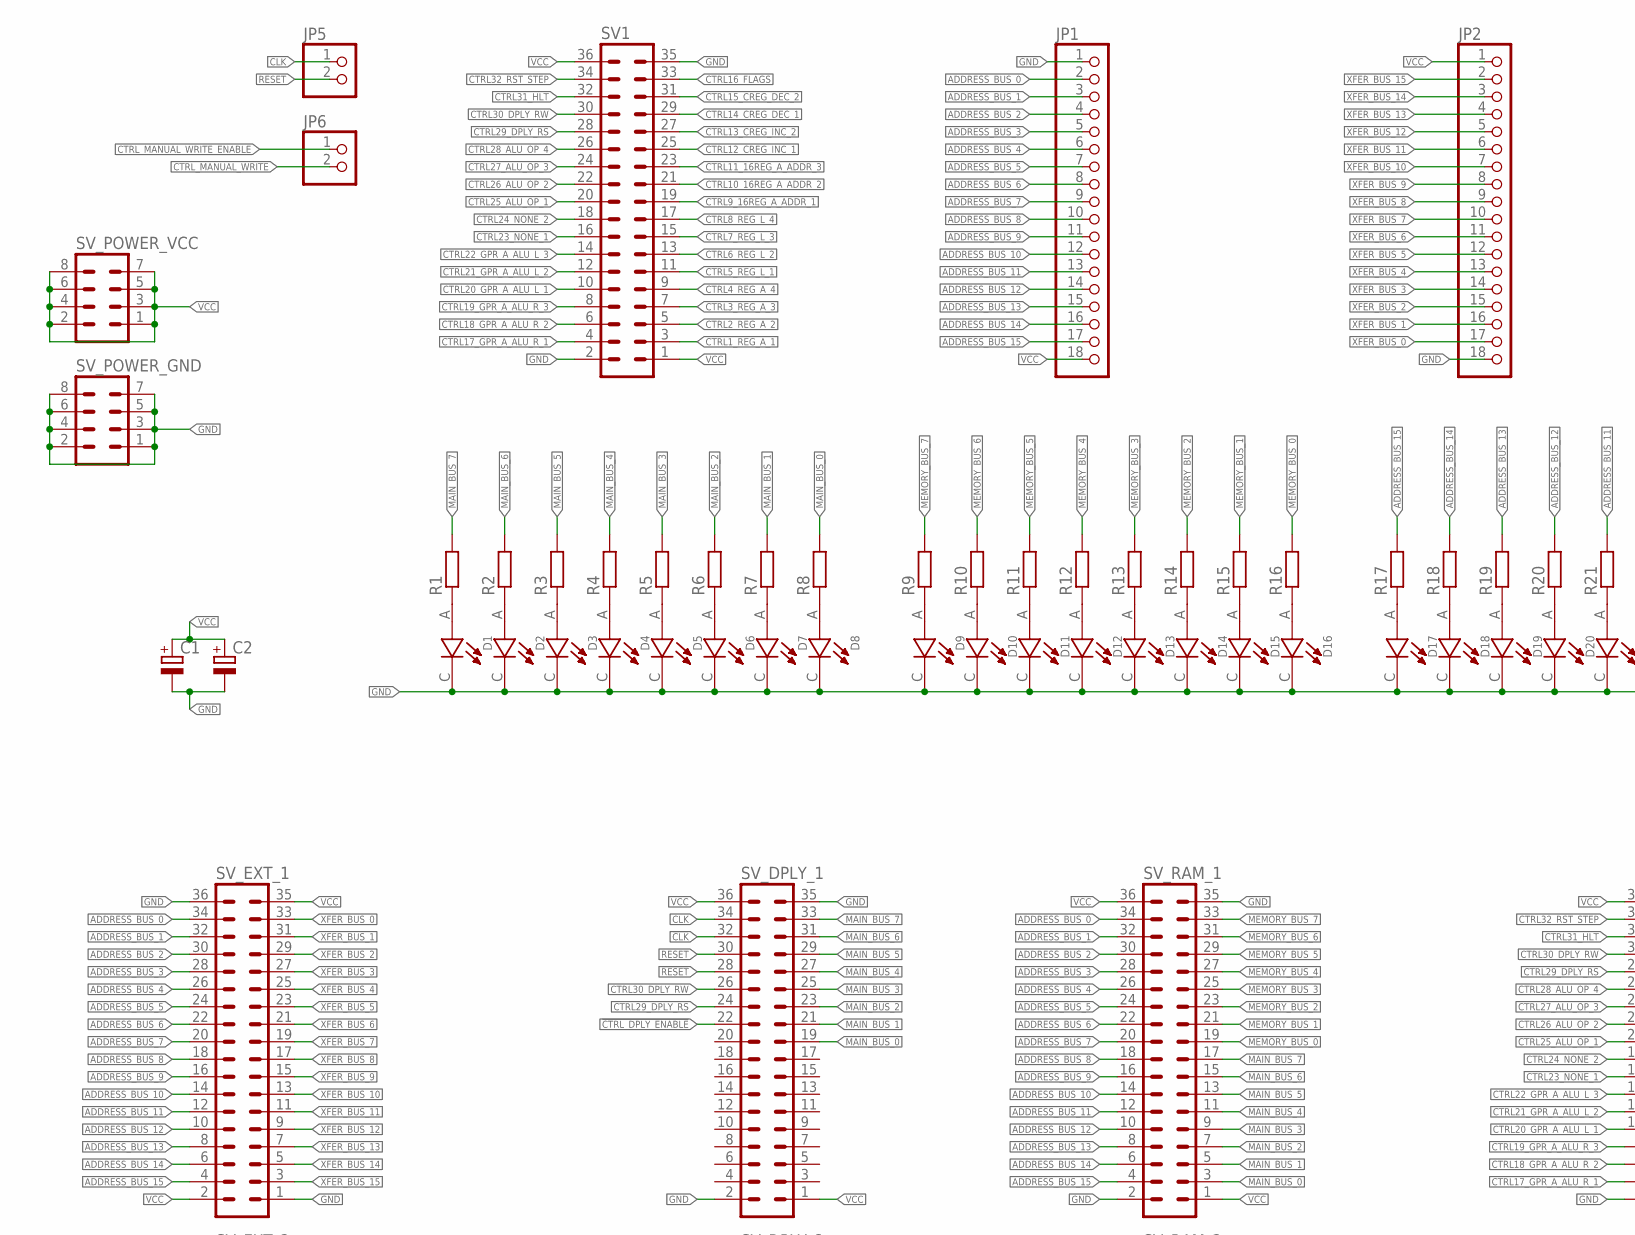
[picture p99: schematic Mainboard_RIGHT.sch, part in row 1, column 1]

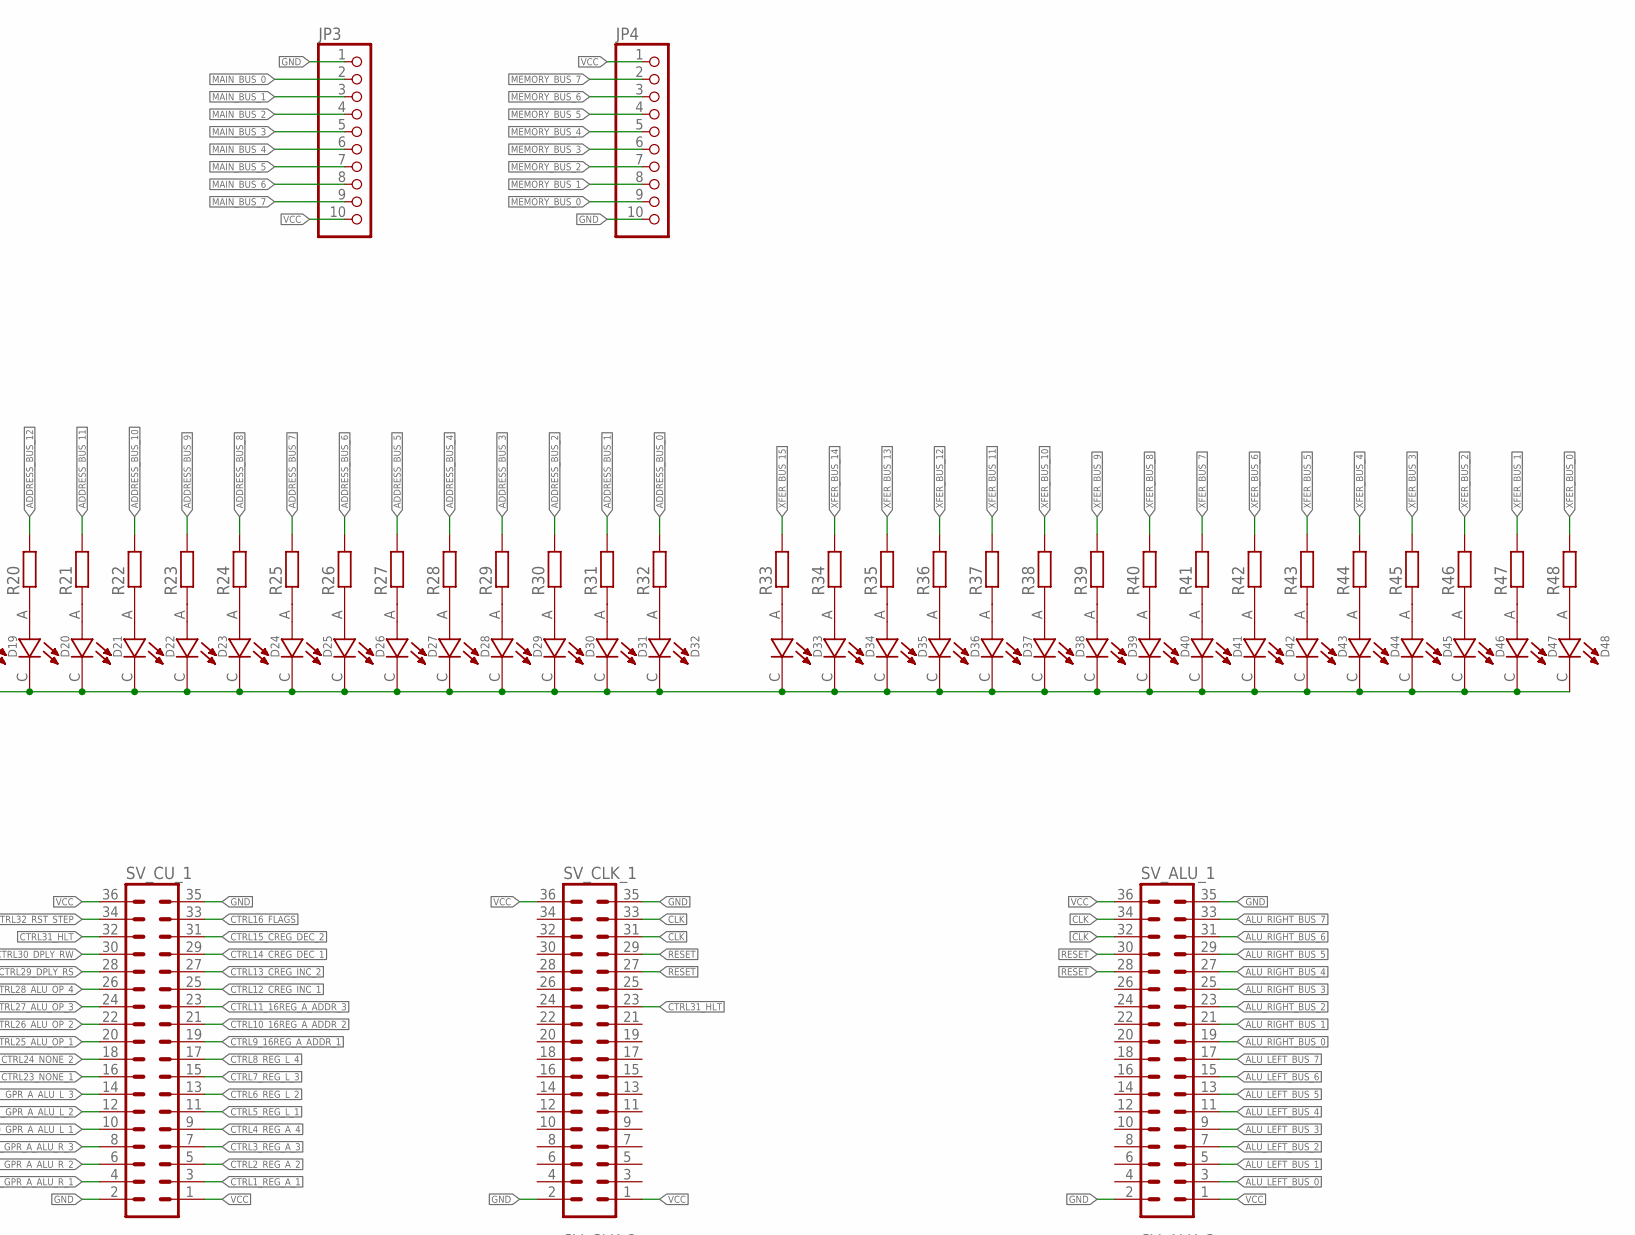
[picture p100: schematic Mainboard_RIGHT.sch, part in row 1, column 2]

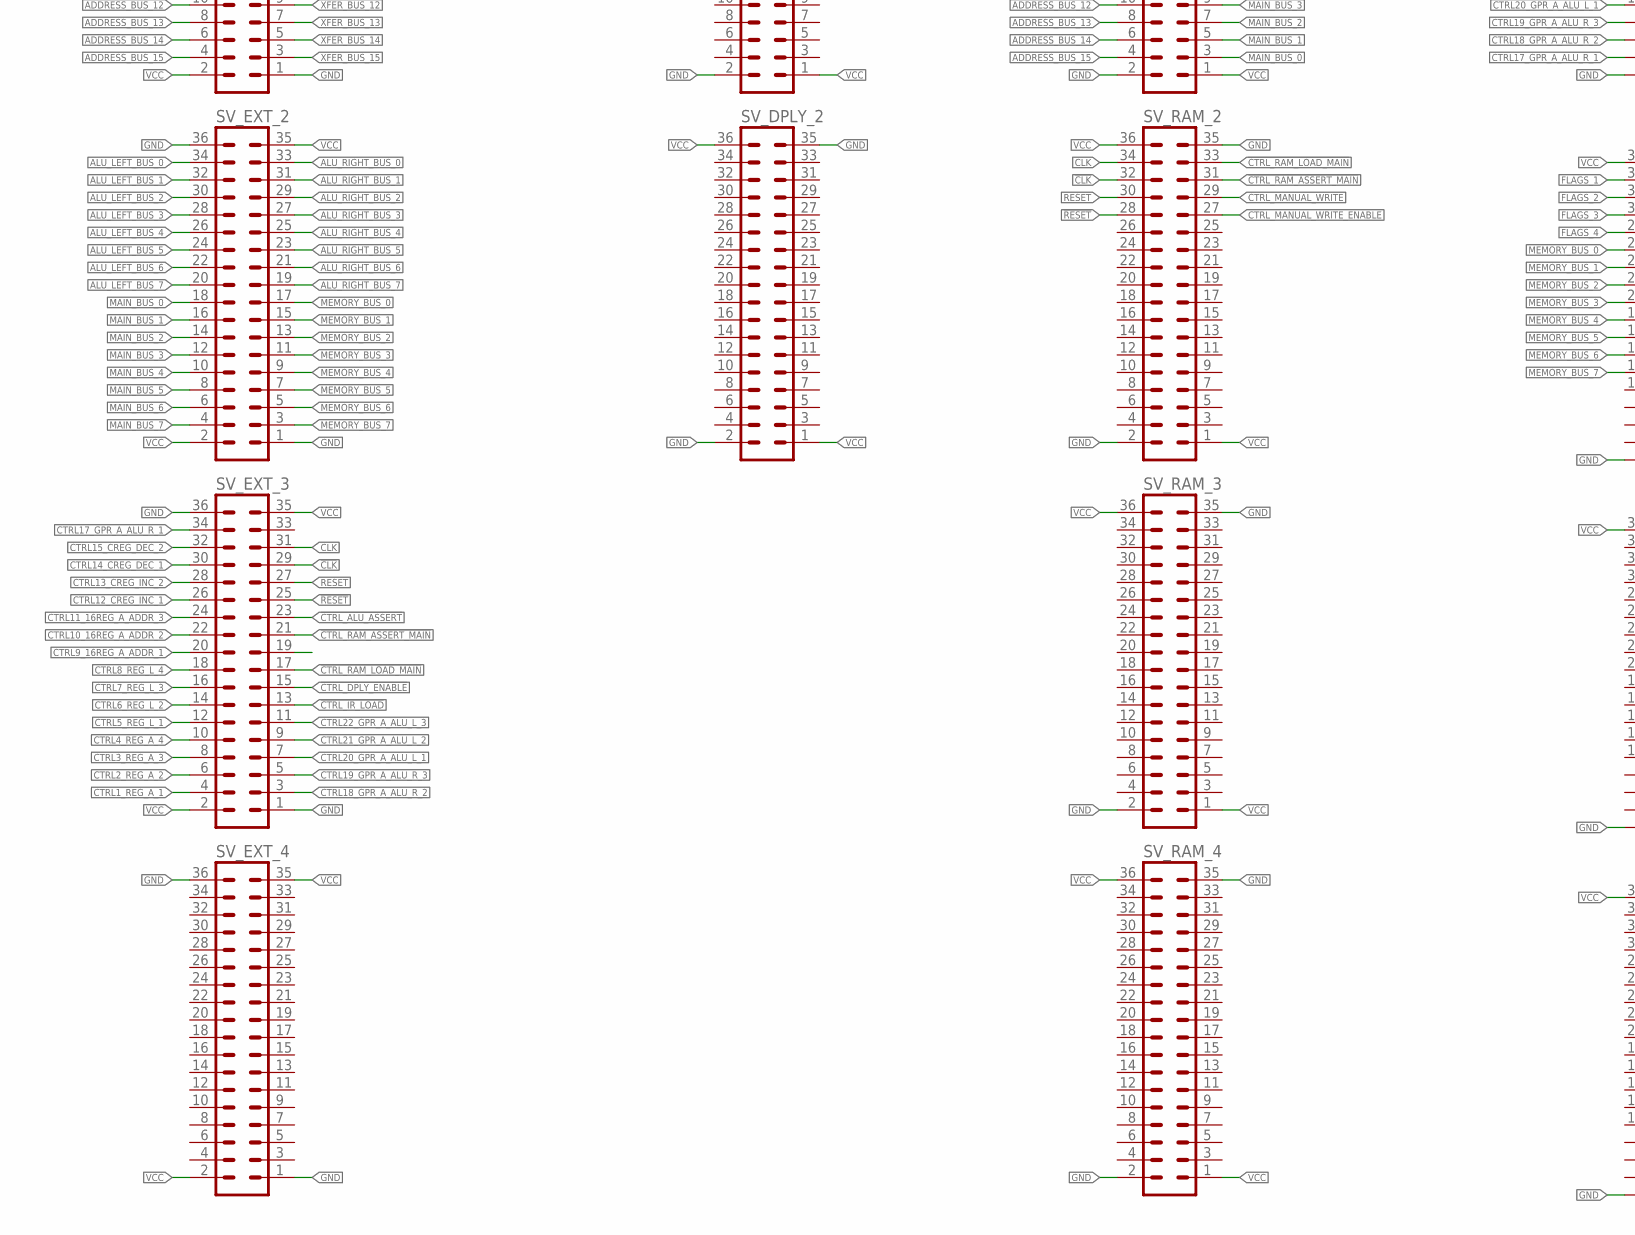
[picture p101: schematic Mainboard_RIGHT.sch, part in row 2, column 1]

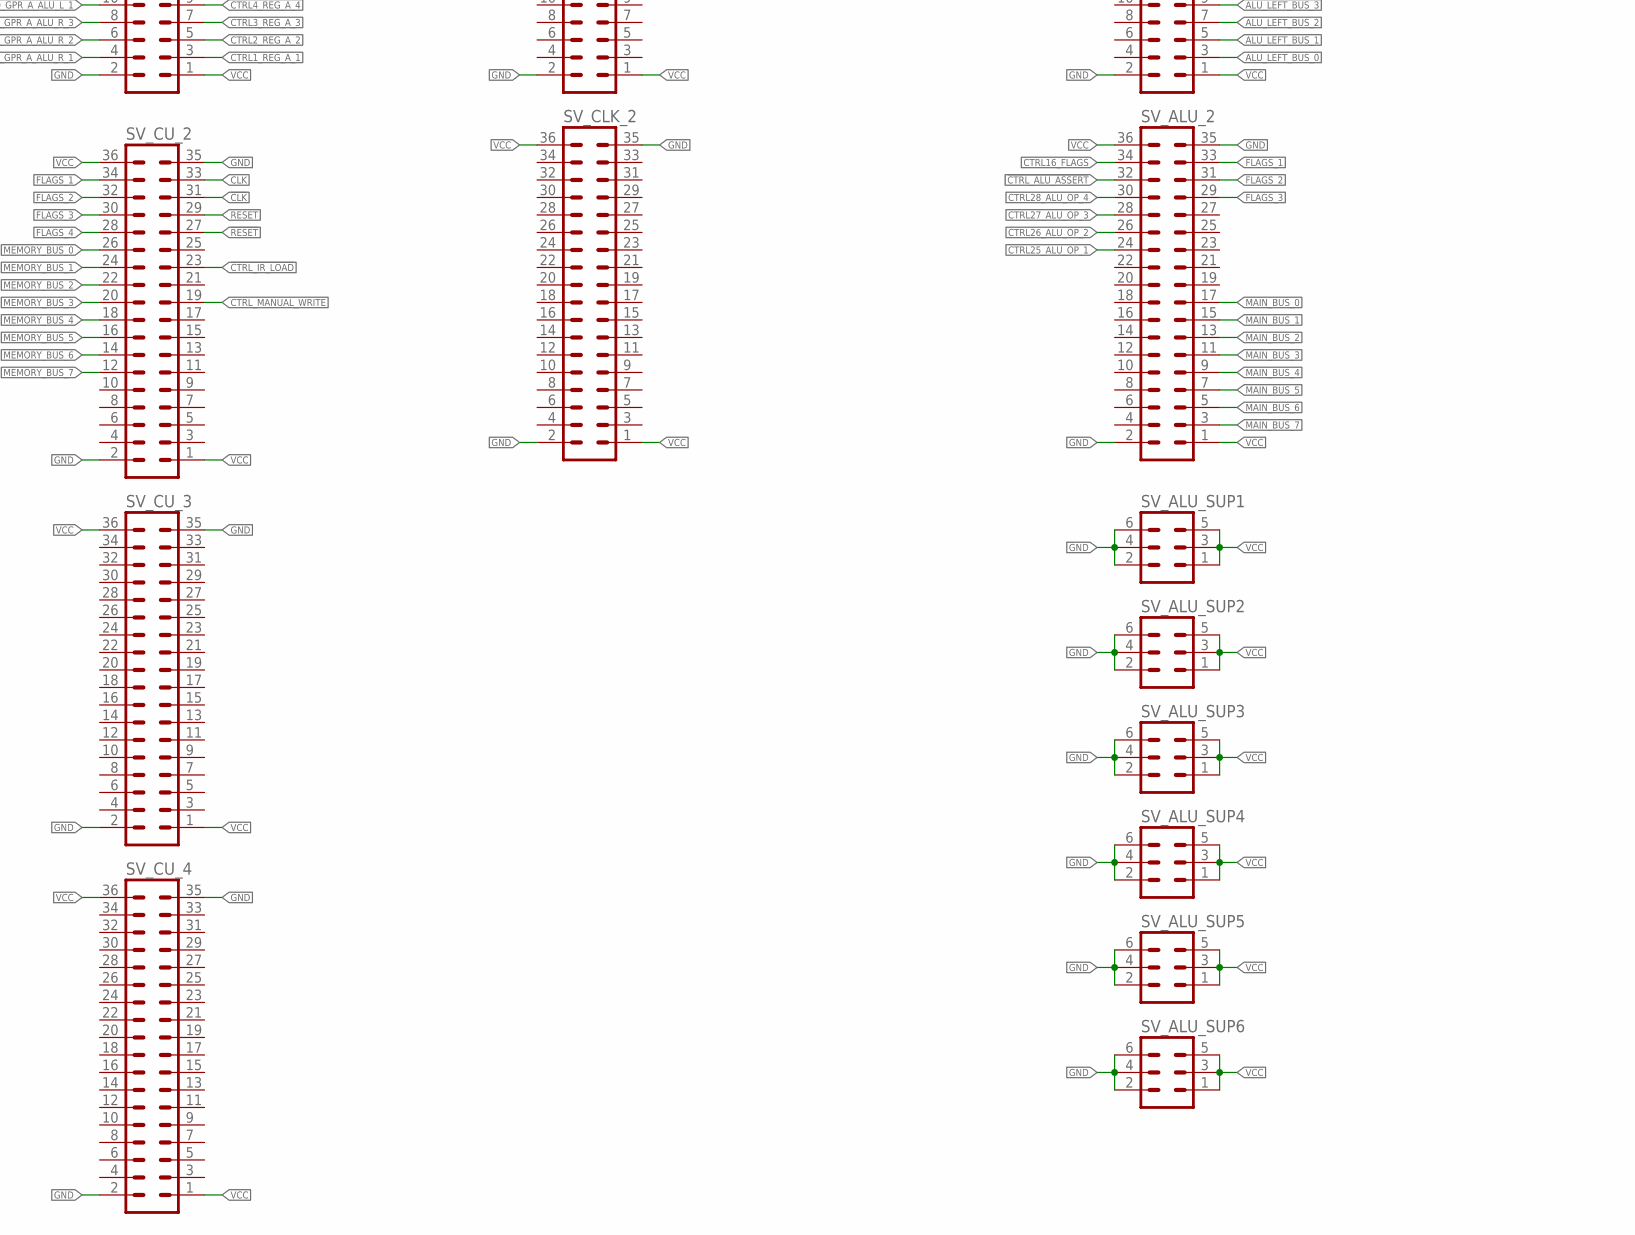
[picture p102: schematic Mainboard_RIGHT.sch, part in row 2, column 2]

Parts:
C1: CPOL-EUE10-20; EB20D
C2: CPOL-EUE5-10.5; E5-10,5
D1, D2, D3, D4, D5, D6, D7, D8, D9, D10, D11, D12, D13, D14, D15, D16, D17, D18, D19, D20, D21, D22, D23, D24, D25, D26, D27, D28, D29, D30, D31, D32, D33, D34, D35, D36, D37, D38, D39, D40, D41, D42, D43, D44, D45, D46, D47, D48: LTST-C193KRKT-5A; LEDC1608X45N
JP1, JP2: PINHD-1X18; 1X18
JP3, JP4: PINHD-1X10; 1X10
JP5, JP6: PINHD-1X2; 1X02
R1, R2, R3, R4, R5, R6, R7, R8, R9, R10, R11, R12, R13, R14, R15, R16, R17, R18, R19, R20, R21, R22, R23, R24, R25, R26, R27, R28, R29, R30, R31, R32, R33, R34, R35, R36, R37, R38, R39, R40, R41, R42, R43, R44, R45, R46, R47, R48: R-EU_R0805; R0805
SV1: MA18-2
SV_ALU_1, SV_ALU_2: MA18-2
SV_ALU_SUP1, SV_ALU_SUP2, SV_ALU_SUP3, SV_ALU_SUP4, SV_ALU_SUP5, SV_ALU_SUP6: MA03-2
SV_CLK_1, SV_CLK_2: MA18-2
SV_CU_1, SV_CU_2, SV_CU_3, SV_CU_4: MA18-2
SV_DPLY_1, SV_DPLY_2: MA18-2
SV_EXT_1, SV_EXT_2, SV_EXT_3, SV_EXT_4: MA18-2W
SV_POWER_GND: MA04-2
SV_POWER_VCC: MA04-2
SV_RAM_1, SV_RAM_2, SV_RAM_3, SV_RAM_4: MA18-2

Connections:
!CLK: SV_ALU_1.32, SV_CLK_1.31, SV_CU_2.31, SV_DPLY_1.32, SV_EXT_3.29, SV_RAM_2.32
!CTRL_ALU_ASSERT: SV_ALU_2.32, SV_EXT_3.23
!CTRL_DPLY_ENABLE: SV_DPLY_1.22, SV_EXT_3.15
!CTRL_IR_LOAD: SV_CU_2.23, SV_EXT_3.13
!CTRL_RAM_ASSERT_MAIN: SV_EXT_3.21, SV_RAM_2.31
!CTRL_RAM_LOAD_MAIN: SV_EXT_3.17, SV_RAM_2.33
!RESET: SV_ALU_1.28, SV_CLK_1.27, SV_CU_2.27, SV_DPLY_1.28, SV_EXT_3.25, SV_RAM_2.28
ADDRESS_BUS_0: JP1.2, R32.2, SV_EXT_1.34, SV_RAM_1.34
ADDRESS_BUS_1: JP1.3, R31.2, SV_EXT_1.32, SV_RAM_1.32
ADDRESS_BUS_2: JP1.4, R30.2, SV_EXT_1.30, SV_RAM_1.30
ADDRESS_BUS_3: JP1.5, R29.2, SV_EXT_1.28, SV_RAM_1.28
ADDRESS_BUS_4: JP1.6, R28.2, SV_EXT_1.26, SV_RAM_1.26
ADDRESS_BUS_5: JP1.7, R27.2, SV_EXT_1.24, SV_RAM_1.24
ADDRESS_BUS_6: JP1.8, R26.2, SV_EXT_1.22, SV_RAM_1.22
ADDRESS_BUS_7: JP1.9, R25.2, SV_EXT_1.20, SV_RAM_1.20
ADDRESS_BUS_8: JP1.10, R24.2, SV_EXT_1.18, SV_RAM_1.18
ADDRESS_BUS_9: JP1.11, R23.2, SV_EXT_1.16, SV_RAM_1.16
ADDRESS_BUS_10: JP1.12, R22.2, SV_EXT_1.14, SV_RAM_1.14
ADDRESS_BUS_11: JP1.13, R21.2, SV_EXT_1.12, SV_RAM_1.12
ADDRESS_BUS_12: JP1.14, R20.2, SV_EXT_1.10, SV_RAM_1.10
ADDRESS_BUS_13: JP1.15, R19.2, SV_EXT_1.8, SV_RAM_1.8
ADDRESS_BUS_14: JP1.16, R18.2, SV_EXT_1.6, SV_RAM_1.6
ADDRESS_BUS_15: JP1.17, R17.2, SV_EXT_1.4, SV_RAM_1.4
ALU_LEFT_BUS_0: SV_ALU_1.3, SV_EXT_2.34
ALU_LEFT_BUS_1: SV_ALU_1.5, SV_EXT_2.32
ALU_LEFT_BUS_2: SV_ALU_1.7, SV_EXT_2.30
ALU_LEFT_BUS_3: SV_ALU_1.9, SV_EXT_2.28
ALU_LEFT_BUS_4: SV_ALU_1.11, SV_EXT_2.26
ALU_LEFT_BUS_5: SV_ALU_1.13, SV_EXT_2.24
ALU_LEFT_BUS_6: SV_ALU_1.15, SV_EXT_2.22
ALU_LEFT_BUS_7: SV_ALU_1.17, SV_EXT_2.20
ALU_RIGHT_BUS_0: SV_ALU_1.19, SV_EXT_2.33
ALU_RIGHT_BUS_1: SV_ALU_1.21, SV_EXT_2.31
ALU_RIGHT_BUS_2: SV_ALU_1.23, SV_EXT_2.29
ALU_RIGHT_BUS_3: SV_ALU_1.25, SV_EXT_2.27
ALU_RIGHT_BUS_4: SV_ALU_1.27, SV_EXT_2.25
ALU_RIGHT_BUS_5: SV_ALU_1.29, SV_EXT_2.23
ALU_RIGHT_BUS_6: SV_ALU_1.31, SV_EXT_2.21
ALU_RIGHT_BUS_7: SV_ALU_1.33, SV_EXT_2.19
CLK: JP5.1, SV_ALU_1.34, SV_CLK_1.33, SV_CU_2.33, SV_DPLY_1.34, SV_EXT_3.31, SV_RAM_2.34
CTRL1_REG_A_1: SV1.3, SV_CU_1.3, SV_EXT_3.4
CTRL2_REG_A_2: SV1.5, SV_CU_1.5, SV_EXT_3.6
CTRL3_REG_A_3: SV1.7, SV_CU_1.7, SV_EXT_3.8
CTRL4_REG_A_4: SV1.9, SV_CU_1.9, SV_EXT_3.10
CTRL5_REG_L_1: SV1.11, SV_CU_1.11, SV_EXT_3.12
CTRL6_REG_L_2: SV1.13, SV_CU_1.13, SV_EXT_3.14
CTRL7_REG_L_3: SV1.15, SV_CU_1.15, SV_EXT_3.16
CTRL8_REG_L_4: SV1.17, SV_CU_1.17, SV_EXT_3.18
CTRL9_16REG_A_ADDR_1: SV1.19, SV_CU_1.19, SV_EXT_3.20
CTRL10_16REG_A_ADDR_2: SV1.21, SV_CU_1.21, SV_EXT_3.22
CTRL11_16REG_A_ADDR_3: SV1.23, SV_CU_1.23, SV_EXT_3.24
CTRL12_CREG_INC_1: SV1.25, SV_CU_1.25, SV_EXT_3.26
CTRL13_CREG_INC_2: SV1.27, SV_CU_1.27, SV_EXT_3.28
CTRL14_CREG_DEC_1: SV1.29, SV_CU_1.29, SV_EXT_3.30
CTRL15_CREG_DEC_2: SV1.31, SV_CU_1.31, SV_EXT_3.32
CTRL16_FLAGS: SV1.33, SV_ALU_2.34, SV_CU_1.33
CTRL17_GPR_A_ALU_R_1: SV1.4, SV_CU_1.4, SV_EXT_3.34
CTRL18_GPR_A_ALU_R_2: SV1.6, SV_CU_1.6, SV_EXT_3.3
CTRL19_GPR_A_ALU_R_3: SV1.8, SV_CU_1.8, SV_EXT_3.5
CTRL20_GPR_A_ALU_L_1: SV1.10, SV_CU_1.10, SV_EXT_3.7
CTRL21_GPR_A_ALU_L_2: SV1.12, SV_CU_1.12, SV_EXT_3.9
CTRL22_GPR_A_ALU_L_3: SV1.14, SV_CU_1.14, SV_EXT_3.11
CTRL23_NONE_1: SV1.16, SV_CU_1.16
CTRL24_NONE_2: SV1.18, SV_CU_1.18
CTRL25_ALU_OP_1: SV1.20, SV_ALU_2.24, SV_CU_1.20
CTRL26_ALU_OP_2: SV1.22, SV_ALU_2.26, SV_CU_1.22
CTRL27_ALU_OP_3: SV1.24, SV_ALU_2.28, SV_CU_1.24
CTRL28_ALU_OP_4: SV1.26, SV_ALU_2.30, SV_CU_1.26
CTRL29_DPLY_RS: SV1.28, SV_CU_1.28, SV_DPLY_1.24
CTRL30_DPLY_RW: SV1.30, SV_CU_1.30, SV_DPLY_1.26
CTRL31_HLT: SV1.32, SV_CLK_1.23, SV_CU_1.32
CTRL32_RST_STEP: SV1.34, SV_CU_1.34
CTRL_MANUAL_WRITE: JP6.2, SV_CU_2.19, SV_RAM_2.29
CTRL_MANUAL_WRITE_ENABLE: JP6.1, SV_RAM_2.27
FLAGS_1: SV_ALU_2.33, SV_CU_2.34
FLAGS_2: SV_ALU_2.31, SV_CU_2.32
FLAGS_3: SV_ALU_2.29, SV_CU_2.30
FLAGS_4: SV_CU_2.28
GND: C1.-, C2.-, D1.C, D2.C, D3.C, D4.C, D5.C, D6.C, D7.C, D8.C, D9.C, D10.C, D11.C, D12.C, D13.C, D14.C, D15.C, D16.C, D17.C, D18.C, D19.C, D20.C, D21.C, D22.C, D23.C, D24.C, D25.C, D26.C, D27.C, D28.C, D29.C, D30.C, D31.C, D32.C, D33.C, D34.C, D35.C, D36.C, D37.C, D38.C, D39.C, D40.C, D41.C, D42.C, D43.C, D44.C, D45.C, D46.C, D47.C, D48.C, JP1.1, JP2.18, JP3.1, JP4.10, SV1.2, SV1.35, SV_ALU_1.2, SV_ALU_1.35, SV_ALU_2.2, SV_ALU_2.35, SV_ALU_SUP1.2, SV_ALU_SUP1.4, SV_ALU_SUP1.6, SV_ALU_SUP2.2, SV_ALU_SUP2.4, SV_ALU_SUP2.6, SV_ALU_SUP3.2, SV_ALU_SUP3.4, SV_ALU_SUP3.6, SV_ALU_SUP4.2, SV_ALU_SUP4.4, SV_ALU_SUP4.6, SV_ALU_SUP5.2, SV_ALU_SUP5.4, SV_ALU_SUP5.6, SV_ALU_SUP6.2, SV_ALU_SUP6.4, SV_ALU_SUP6.6, SV_CLK_1.2, SV_CLK_1.35, SV_CLK_2.2, SV_CLK_2.35, SV_CU_1.2, SV_CU_1.35, SV_CU_2.2, SV_CU_2.35, SV_CU_3.2, SV_CU_3.35, SV_CU_4.2, SV_CU_4.35, SV_DPLY_1.2, SV_DPLY_1.35, SV_DPLY_2.2, SV_DPLY_2.35, SV_EXT_1.1, SV_EXT_1.36, SV_EXT_2.1, SV_EXT_2.36, SV_EXT_3.1, SV_EXT_3.36, SV_EXT_4.1, SV_EXT_4.36, SV_POWER_GND.1, SV_POWER_GND.2, SV_POWER_GND.3, SV_POWER_GND.4, SV_POWER_GND.5, SV_POWER_GND.6, SV_POWER_GND.7, SV_POWER_GND.8, SV_RAM_1.2, SV_RAM_1.35, SV_RAM_2.2, SV_RAM_2.35, SV_RAM_3.2, SV_RAM_3.35, SV_RAM_4.2, SV_RAM_4.35
MAIN_BUS_0: JP3.2, R8.2, SV_ALU_2.17, SV_DPLY_1.19, SV_EXT_2.18, SV_RAM_1.3
MAIN_BUS_1: JP3.3, R7.2, SV_ALU_2.15, SV_DPLY_1.21, SV_EXT_2.16, SV_RAM_1.5
MAIN_BUS_2: JP3.4, R6.2, SV_ALU_2.13, SV_DPLY_1.23, SV_EXT_2.14, SV_RAM_1.7
MAIN_BUS_3: JP3.5, R5.2, SV_ALU_2.11, SV_DPLY_1.25, SV_EXT_2.12, SV_RAM_1.9
MAIN_BUS_4: JP3.6, R4.2, SV_ALU_2.9, SV_DPLY_1.27, SV_EXT_2.10, SV_RAM_1.11
MAIN_BUS_5: JP3.7, R3.2, SV_ALU_2.7, SV_DPLY_1.29, SV_EXT_2.8, SV_RAM_1.13
MAIN_BUS_6: JP3.8, R2.2, SV_ALU_2.5, SV_DPLY_1.31, SV_EXT_2.6, SV_RAM_1.15
MAIN_BUS_7: JP3.9, R1.2, SV_ALU_2.3, SV_DPLY_1.33, SV_EXT_2.4, SV_RAM_1.17
MEMORY_BUS_0: JP4.9, R16.2, SV_CU_2.26, SV_EXT_2.17, SV_RAM_1.19
MEMORY_BUS_1: JP4.8, R15.2, SV_CU_2.24, SV_EXT_2.15, SV_RAM_1.21
MEMORY_BUS_2: JP4.7, R14.2, SV_CU_2.22, SV_EXT_2.13, SV_RAM_1.23
MEMORY_BUS_3: JP4.6, R13.2, SV_CU_2.20, SV_EXT_2.11, SV_RAM_1.25
MEMORY_BUS_4: JP4.5, R12.2, SV_CU_2.18, SV_EXT_2.9, SV_RAM_1.27
MEMORY_BUS_5: JP4.4, R11.2, SV_CU_2.16, SV_EXT_2.7, SV_RAM_1.29
MEMORY_BUS_6: JP4.3, R10.2, SV_CU_2.14, SV_EXT_2.5, SV_RAM_1.31
MEMORY_BUS_7: JP4.2, R9.2, SV_CU_2.12, SV_EXT_2.3, SV_RAM_1.33
unnamed: D1.A, R1.1
unnamed: D2.A, R2.1
unnamed: D3.A, R3.1
unnamed: D4.A, R4.1
unnamed: D5.A, R5.1
unnamed: D6.A, R6.1
unnamed: D7.A, R7.1
unnamed: D8.A, R8.1
unnamed: D9.A, R9.1
unnamed: D10.A, R10.1
unnamed: D11.A, R11.1
unnamed: D12.A, R12.1
unnamed: D13.A, R13.1
unnamed: D14.A, R14.1
unnamed: D15.A, R15.1
unnamed: D16.A, R16.1
unnamed: D17.A, R17.1
unnamed: D18.A, R18.1
unnamed: D19.A, R19.1
unnamed: D20.A, R20.1
unnamed: D21.A, R21.1
unnamed: D22.A, R22.1
unnamed: D23.A, R23.1
unnamed: D24.A, R24.1
unnamed: D25.A, R25.1
unnamed: D26.A, R26.1
unnamed: D27.A, R27.1
unnamed: D28.A, R28.1
unnamed: D29.A, R29.1
unnamed: D30.A, R30.1
unnamed: D31.A, R31.1
unnamed: D32.A, R32.1
unnamed: D33.A, R33.1
unnamed: D34.A, R34.1
unnamed: D35.A, R35.1
unnamed: D36.A, R36.1
unnamed: D37.A, R37.1
unnamed: D38.A, R38.1
unnamed: D39.A, R39.1
unnamed: D40.A, R40.1
unnamed: D41.A, R41.1
unnamed: D42.A, R42.1
unnamed: D43.A, R43.1
unnamed: D44.A, R44.1
unnamed: D45.A, R45.1
unnamed: D46.A, R46.1
unnamed: D47.A, R47.1
unnamed: D48.A, R48.1
RESET: JP5.2, SV_ALU_1.30, SV_CLK_1.29, SV_CU_2.29, SV_DPLY_1.30, SV_EXT_3.27, SV_RAM_2.30
VCC: C1.+, C2.+, JP1.18, JP2.1, JP3.10, JP4.1, SV1.1, SV1.36, SV_ALU_1.1, SV_ALU_1.36, SV_ALU_2.1, SV_ALU_2.36, SV_ALU_SUP1.1, SV_ALU_SUP1.3, SV_ALU_SUP1.5, SV_ALU_SUP2.1, SV_ALU_SUP2.3, SV_ALU_SUP2.5, SV_ALU_SUP3.1, SV_ALU_SUP3.3, SV_ALU_SUP3.5, SV_ALU_SUP4.1, SV_ALU_SUP4.3, SV_ALU_SUP4.5, SV_ALU_SUP5.1, SV_ALU_SUP5.3, SV_ALU_SUP5.5, SV_ALU_SUP6.1, SV_ALU_SUP6.3, SV_ALU_SUP6.5, SV_CLK_1.1, SV_CLK_1.36, SV_CLK_2.1, SV_CLK_2.36, SV_CU_1.1, SV_CU_1.36, SV_CU_2.1, SV_CU_2.36, SV_CU_3.1, SV_CU_3.36, SV_CU_4.1, SV_CU_4.36, SV_DPLY_1.1, SV_DPLY_1.36, SV_DPLY_2.1, SV_DPLY_2.36, SV_EXT_1.2, SV_EXT_1.35, SV_EXT_2.2, SV_EXT_2.35, SV_EXT_3.2, SV_EXT_3.35, SV_EXT_4.2, SV_EXT_4.35, SV_POWER_VCC.1, SV_POWER_VCC.2, SV_POWER_VCC.3, SV_POWER_VCC.4, SV_POWER_VCC.5, SV_POWER_VCC.6, SV_POWER_VCC.7, SV_POWER_VCC.8, SV_RAM_1.1, SV_RAM_1.36, SV_RAM_2.1, SV_RAM_2.36, SV_RAM_3.1, SV_RAM_3.36, SV_RAM_4.1, SV_RAM_4.36
XFER_BUS_0: JP2.17, R48.2, SV_EXT_1.33
XFER_BUS_1: JP2.16, R47.2, SV_EXT_1.31
XFER_BUS_2: JP2.15, R46.2, SV_EXT_1.29
XFER_BUS_3: JP2.14, R45.2, SV_EXT_1.27
XFER_BUS_4: JP2.13, R44.2, SV_EXT_1.25
XFER_BUS_5: JP2.12, R43.2, SV_EXT_1.23
XFER_BUS_6: JP2.11, R42.2, SV_EXT_1.21
XFER_BUS_7: JP2.10, R41.2, SV_EXT_1.19
XFER_BUS_8: JP2.9, R40.2, SV_EXT_1.17
XFER_BUS_9: JP2.8, R39.2, SV_EXT_1.15
XFER_BUS_10: JP2.7, R38.2, SV_EXT_1.13
XFER_BUS_11: JP2.6, R37.2, SV_EXT_1.11
XFER_BUS_12: JP2.5, R36.2, SV_EXT_1.9
XFER_BUS_13: JP2.4, R35.2, SV_EXT_1.7
XFER_BUS_14: JP2.3, R34.2, SV_EXT_1.5
XFER_BUS_15: JP2.2, R33.2, SV_EXT_1.3
