Dargonrol/processor-dev/Dragon/Dragon_4/PCBs/Main Board/Mainboard_RIGHT.brd

## EAGLE design Dragon/Dragon_4/PCBs/Main Board/Mainboard_RIGHT.brd (continued)

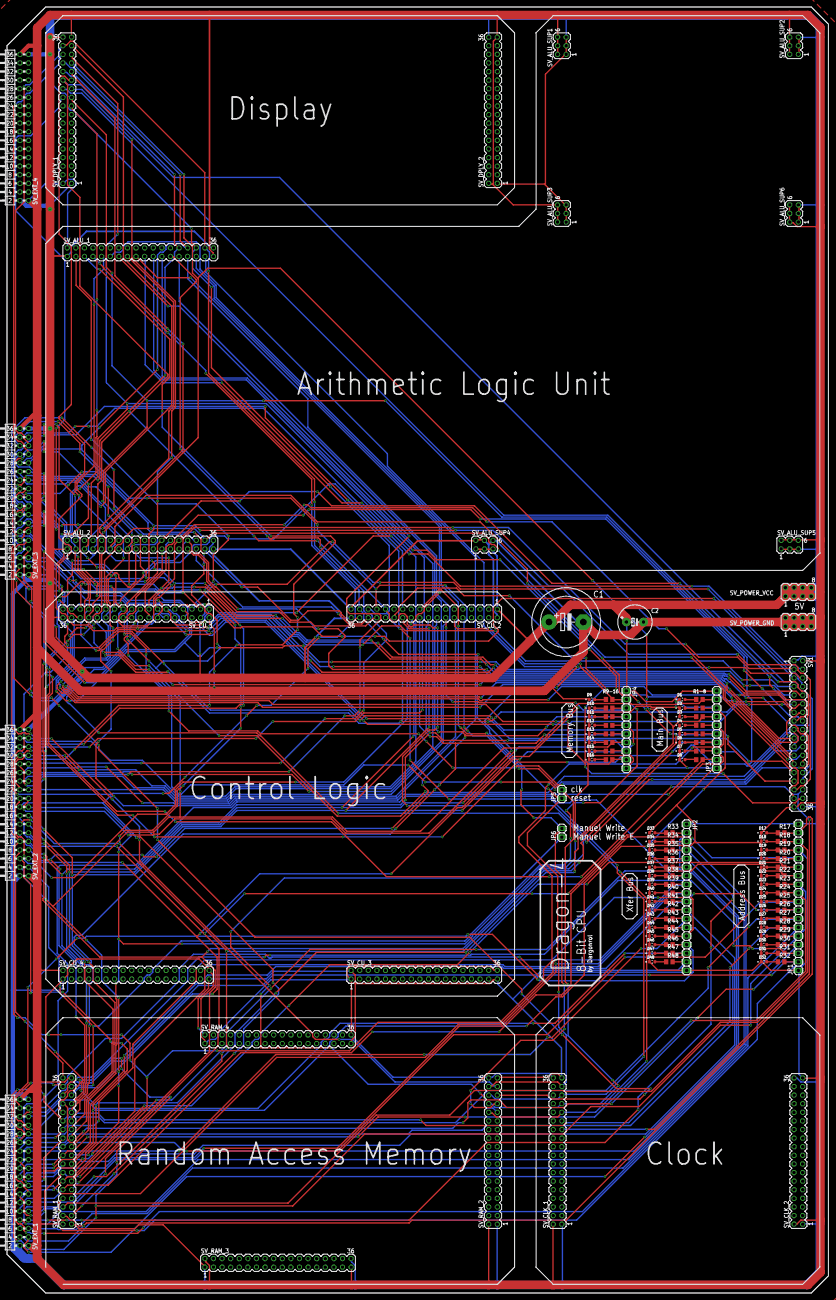
[picture p103: board Mainboard_RIGHT.brd from above]

Board: 2 copper layers, 242.6 x 379.7 mm, 131 parts (0 on the bottom side), 160 nets.
