Dargonrol/processor-dev/Dragon/Dragon_4/PCBs/Clock module/clock.brd

## EAGLE design Dragon/Dragon_4/PCBs/Clock module/clock.brd (2025-08-28)

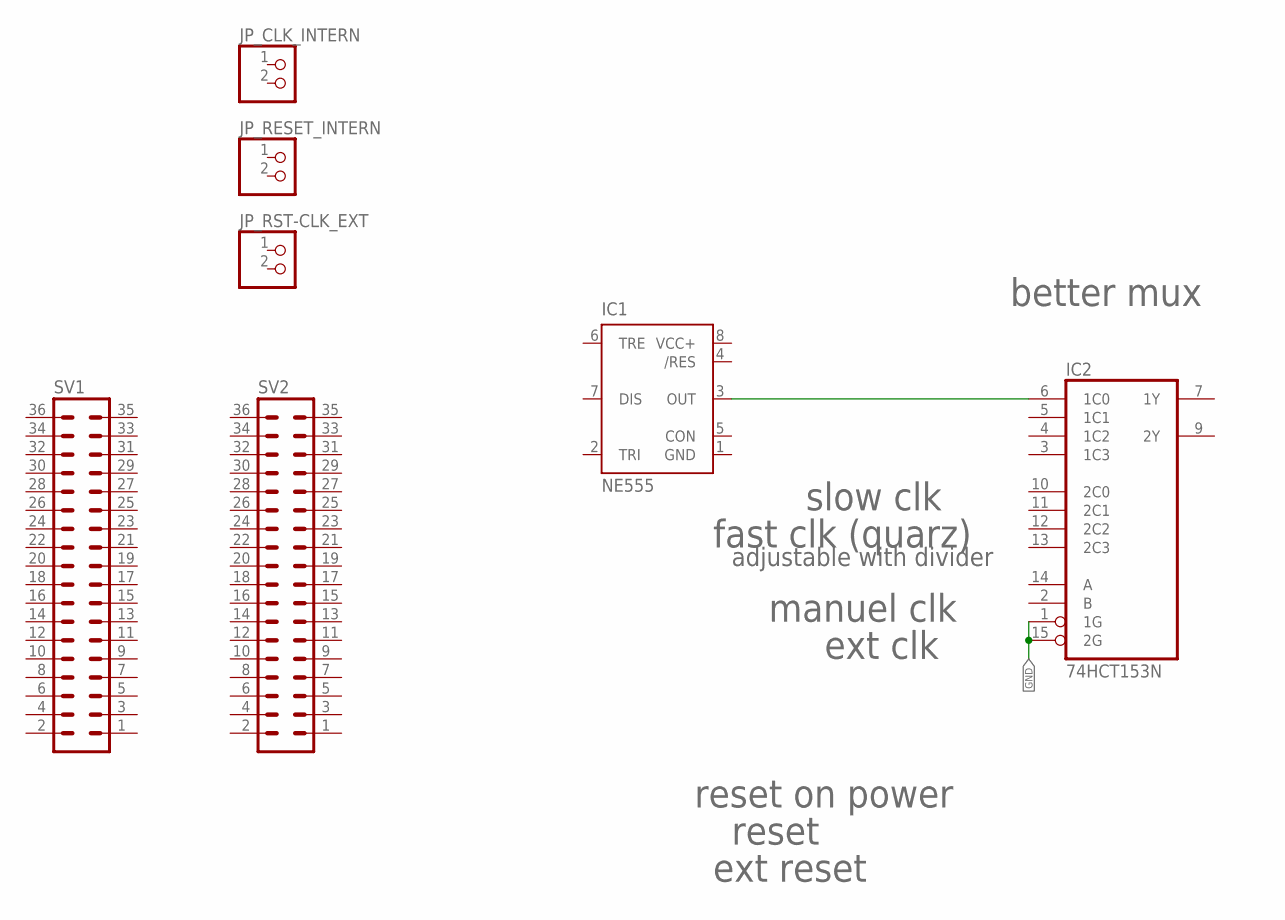
[picture p104: schematic clock.sch]

Parts:
IC1: NE555; DIL-08
IC2: 74HCT153N; DIL16
JP_CLK_INTERN: PINHD-1X2; 1X02
JP_RESET_INTERN: PINHD-1X2; 1X02
JP_RST-CLK_EXT: PINHD-1X2; 1X02
SV1, SV2: MA18-2

Connections:
GND: IC1.1 (GND), IC2.1 (1G), IC2.8 (GND), IC2.15 (2G)
unnamed: IC1.3 (OUT), IC2.6 (1C0)
VCC: IC2.16 (VCC)
VCC+: IC1.8 (VCC+)

Notes on the sheet:
better mux
slow clk
fast clk (quarz)
adjustable with divider
manuel clk
ext clk
reset on power
reset
ext reset

Board: 2 copper layers, 7 parts (0 on the bottom side), 2 nets, no tracks yet.
