Dargonrol/processor-dev/Dragon/Dragon_4/Software/TommyPROM-master/hardware/TommyPROM-8755A Nano.sch

## EAGLE design Dragon/Dragon_4/Software/TommyPROM-master/hardware/TommyPROM-8755A Nano.sch (2024-06-28)

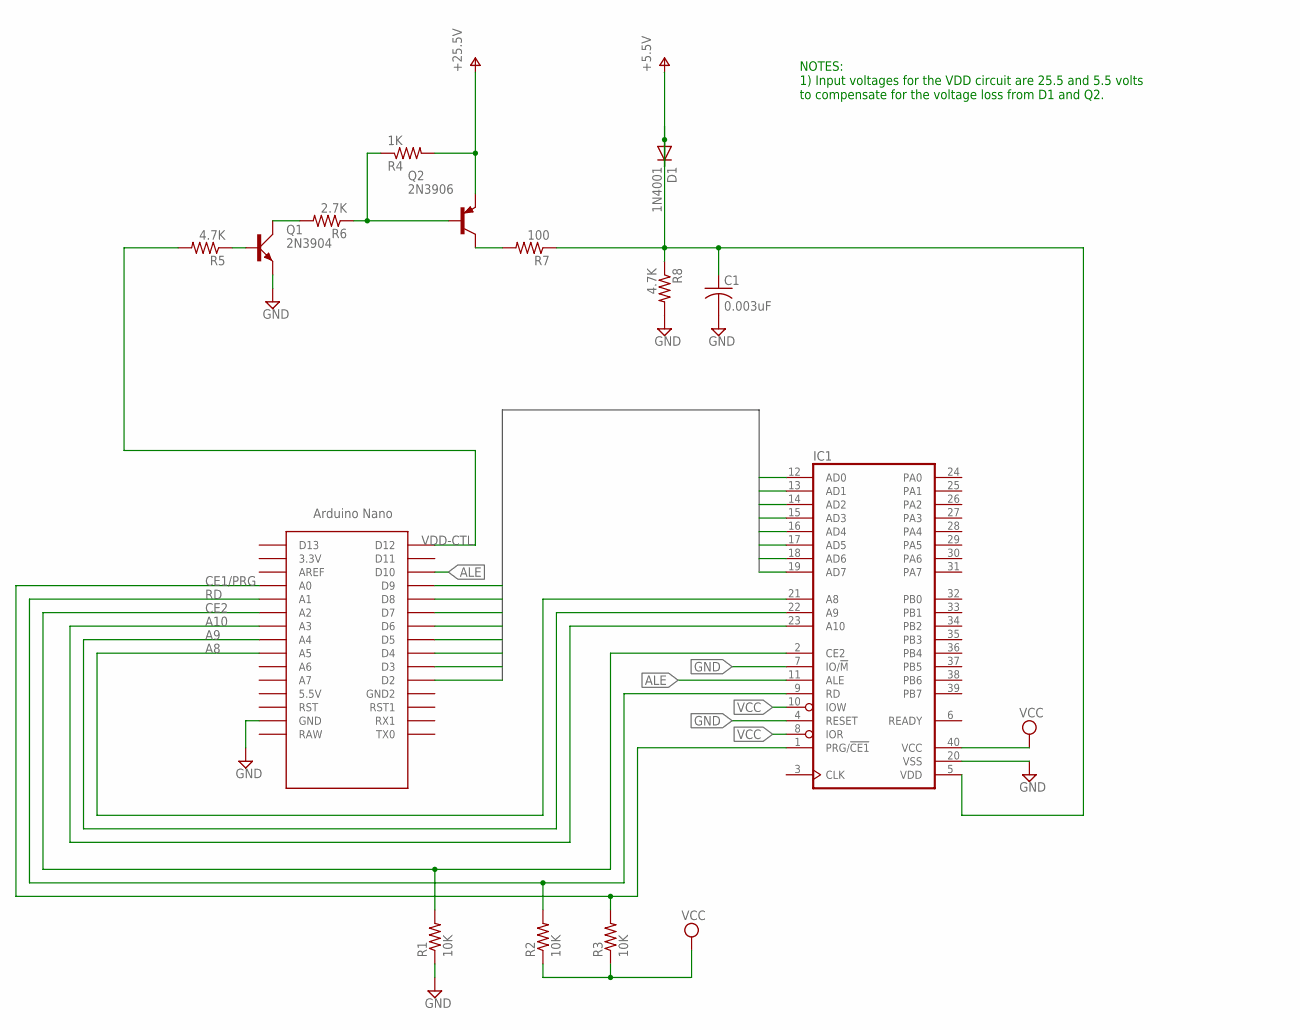
[picture p105: schematic TommyPROM-8755A Nano.sch]

Parts:
C1: 0.003uF; C025-024X044
D1: 1N4001; DO41-10
IC1: 8755; DIL40
Q1: 2N3904; TO92D
Q2: 2N3906; TO92
R1, R2, R3: 10K; 0204/5
R4: 1K; 0204/5
R5, R8: 4.7K; 0204/5
R6: 2.7K; 0204/5
R7: 100; 0204/5
U$2: NANO

Connections:
A8: IC1.21 (A8), U$2.A5
A9: IC1.22 (A9), U$2.A4
A10: IC1.23 (A10), U$2.A3
ALE: IC1.11 (ALE), U$2.D10
CE1/PRG: IC1.1 (PRG/!CE1), R3.2, U$2.A0
CE2: IC1.2 (CE2), R1.2, U$2.A2
D0: IC1.12 (AD0), U$2.D2
D1: IC1.13 (AD1), U$2.D3
D2: IC1.14 (AD2), U$2.D4
D3: IC1.15 (AD3), U$2.D5
D4: IC1.16 (AD4), U$2.D6
D5: IC1.17 (AD5), U$2.D7
D6: IC1.18 (AD6), U$2.D8
D7: IC1.19 (AD7), U$2.D9
GND: C1.2, IC1.4 (RESET), IC1.7 (IO/!M), IC1.20 (VSS), Q1.E, R1.1, R8.2, U$2.GND
unnamed: Q2.1 (C), R7.2
unnamed: Q1.B, R5.1
unnamed: Q2.2 (B), R4.1, R6.1
unnamed: Q1.C, R6.2
RD: IC1.9 (RD), R2.2, U$2.A1
V+: C1.1, D1.A, D1.C, IC1.5 (VDD), Q2.3 (E), R4.2, R7.1, R8.1
VCC: IC1.8 (IOR), IC1.10 (IOW), IC1.40 (VCC), R2.1, R3.1
VDD-CTL: R5.2, U$2.D12

Notes on the sheet:
NOTES: 1) Input voltages for the VDD circuit are 25.5 and 5.5 volts to compensate for the voltage loss from D1 and Q2.
